shufps/eload2/images/PXL_20251216_090533911.jpg

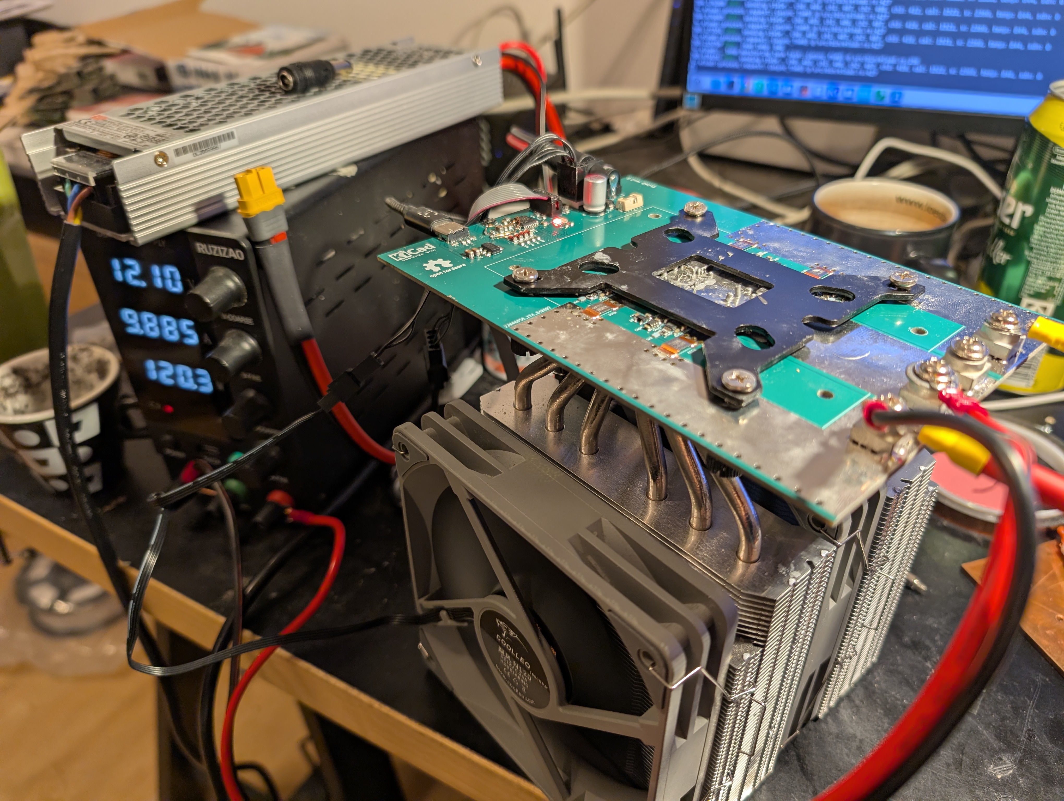
images/PXL_20251216_090533911.jpg
