shufps/eload2/firmware/stm32-metapac/src/chips/metadata_0062.rs

                pub(crate) static PERIPHERALS: &'static [Peripheral] = &[
    Peripheral {
        name: "ADC1",
        address: 1073816576,
        registers: Some(
            PeripheralRegisters {
                kind: "adc",
                version: "f1",
                block: "ADC",
                ir: &adc::REGISTERS,
            },
        ),
        rcc: Some(
            PeripheralRcc {
                clock: "pclk2",
                enable: Some(
                    PeripheralRccRegister {
                        register: "apb2enr",
                        field: "adc1en",
                    },
                ),
                reset: Some(
                    PeripheralRccRegister {
                        register: "apb2rstr",
                        field: "adc1rst",
                    },
                ),
                mux: None,
                stop_mode: StopMode::Stop1,
            },
        ),
        pins: &[
            PeripheralPin {
                pin: "PA0",
                signal: "IN0",
                af: None,
            },
            PeripheralPin {
                pin: "PA1",
                signal: "IN1",
                af: None,
            },
            PeripheralPin {
                pin: "PA2",
                signal: "IN2",
                af: None,
            },
            PeripheralPin {
                pin: "PA3",
                signal: "IN3",
                af: None,
            },
            PeripheralPin {
                pin: "PA4",
                signal: "IN4",
                af: None,
            },
            PeripheralPin {
                pin: "PA5",
                signal: "IN5",
                af: None,
            },
            PeripheralPin {
                pin: "PA6",
                signal: "IN6",
                af: None,
            },
            PeripheralPin {
                pin: "PA7",
                signal: "IN7",
                af: None,
            },
            PeripheralPin {
                pin: "PB0",
                signal: "IN8",
                af: None,
            },
            PeripheralPin {
                pin: "PB1",
                signal: "IN9",
                af: None,
            },
        ],
        dma_channels: &[
            PeripheralDmaChannel {
                signal: "ADC1",
                channel: Some(
                    "DMA1_CH1",
                ),
                dmamux: None,
                dma: None,
                request: None,
            },
        ],
        interrupts: &[
            PeripheralInterrupt {
                signal: "GLOBAL",
                interrupt: "ADC1",
            },
        ],
    },
    Peripheral {
        name: "ADC_COMMON",
        address: 1073816576,
        registers: None,
        rcc: None,
        pins: &[],
        dma_channels: &[],
        interrupts: &[],
    },
    Peripheral {
        name: "AFIO",
        address: 1073807360,
        registers: Some(
            PeripheralRegisters {
                kind: "afio",
                version: "f1",
                block: "AFIO",
                ir: &afio::REGISTERS,
            },
        ),
        rcc: Some(
            PeripheralRcc {
                clock: "pclk2",
                enable: Some(
                    PeripheralRccRegister {
                        register: "apb2enr",
                        field: "afioen",
                    },
                ),
                reset: Some(
                    PeripheralRccRegister {
                        register: "apb2rstr",
                        field: "afiorst",
                    },
                ),
                mux: None,
                stop_mode: StopMode::Stop1,
            },
        ),
        pins: &[],
        dma_channels: &[],
        interrupts: &[],
    },
    Peripheral {
        name: "BKP",
        address: 1073769472,
        registers: Some(
            PeripheralRegisters {
                kind: "bkp",
                version: "v1",
                block: "BKP",
                ir: &bkp::REGISTERS,
            },
        ),
        rcc: Some(
            PeripheralRcc {
                clock: "pclk1",
                enable: Some(
                    PeripheralRccRegister {
                        register: "apb1enr",
                        field: "bkpen",
                    },
                ),
                reset: Some(
                    PeripheralRccRegister {
                        register: "apb1rstr",
                        field: "bkprst",
                    },
                ),
                mux: None,
                stop_mode: StopMode::Stop1,
            },
        ),
        pins: &[],
        dma_channels: &[],
        interrupts: &[],
    },
    Peripheral {
        name: "CEC",
        address: 1073772544,
        registers: None,
        rcc: Some(
            PeripheralRcc {
                clock: "pclk1",
                enable: Some(
                    PeripheralRccRegister {
                        register: "apb1enr",
                        field: "cecen",
                    },
                ),
                reset: Some(
                    PeripheralRccRegister {
                        register: "apb1rstr",
                        field: "cecrst",
                    },
                ),
                mux: None,
                stop_mode: StopMode::Stop1,
            },
        ),
        pins: &[],
        dma_channels: &[],
        interrupts: &[],
    },
    Peripheral {
        name: "CRC",
        address: 1073885184,
        registers: Some(
            PeripheralRegisters {
                kind: "crc",
                version: "v1",
                block: "CRC",
                ir: &crc::REGISTERS,
            },
        ),
        rcc: Some(
            PeripheralRcc {
                clock: "hclk1",
                enable: Some(
                    PeripheralRccRegister {
                        register: "ahbenr",
                        field: "crcen",
                    },
                ),
                reset: None,
                mux: None,
                stop_mode: StopMode::Stop1,
            },
        ),
        pins: &[],
        dma_channels: &[],
        interrupts: &[],
    },
    Peripheral {
        name: "DAC",
        address: 1073771520,
        registers: Some(
            PeripheralRegisters {
                kind: "dac",
                version: "v2",
                block: "DAC",
                ir: &dac::REGISTERS,
            },
        ),
        rcc: Some(
            PeripheralRcc {
                clock: "pclk1",
                enable: Some(
                    PeripheralRccRegister {
                        register: "apb1enr",
                        field: "dacen",
                    },
                ),
                reset: Some(
                    PeripheralRccRegister {
                        register: "apb1rstr",
                        field: "dacrst",
                    },
                ),
                mux: None,
                stop_mode: StopMode::Stop1,
            },
        ),
        pins: &[
            PeripheralPin {
                pin: "PA4",
                signal: "OUT1",
                af: None,
            },
            PeripheralPin {
                pin: "PA5",
                signal: "OUT2",
                af: None,
            },
        ],
        dma_channels: &[
            PeripheralDmaChannel {
                signal: "CH1",
                channel: Some(
                    "DMA1_CH3",
                ),
                dmamux: None,
                dma: None,
                request: None,
            },
            PeripheralDmaChannel {
                signal: "CH2",
                channel: Some(
                    "DMA1_CH4",
                ),
                dmamux: None,
                dma: None,
                request: None,
            },
        ],
        interrupts: &[
            PeripheralInterrupt {
                signal: "GLOBAL",
                interrupt: "TIM6_DAC",
            },
        ],
    },
    Peripheral {
        name: "DBGMCU",
        address: 3758366720,
        registers: Some(
            PeripheralRegisters {
                kind: "dbgmcu",
                version: "f1",
                block: "DBGMCU",
                ir: &dbgmcu::REGISTERS,
            },
        ),
        rcc: None,
        pins: &[],
        dma_channels: &[],
        interrupts: &[],
    },
    Peripheral {
        name: "DMA1",
        address: 1073872896,
        registers: Some(
            PeripheralRegisters {
                kind: "bdma",
                version: "v1",
                block: "DMA",
                ir: &bdma::REGISTERS,
            },
        ),
        rcc: Some(
            PeripheralRcc {
                clock: "hclk1",
                enable: Some(
                    PeripheralRccRegister {
                        register: "ahbenr",
                        field: "dma1en",
                    },
                ),
                reset: None,
                mux: None,
                stop_mode: StopMode::Stop1,
            },
        ),
        pins: &[],
        dma_channels: &[],
        interrupts: &[
            PeripheralInterrupt {
                signal: "CH1",
                interrupt: "DMA1_CHANNEL1",
            },
            PeripheralInterrupt {
                signal: "CH2",
                interrupt: "DMA1_CHANNEL2",
            },
            PeripheralInterrupt {
                signal: "CH3",
                interrupt: "DMA1_CHANNEL3",
            },
            PeripheralInterrupt {
                signal: "CH4",
                interrupt: "DMA1_CHANNEL4",
            },
            PeripheralInterrupt {
                signal: "CH5",
                interrupt: "DMA1_CHANNEL5",
            },
            PeripheralInterrupt {
                signal: "CH6",
                interrupt: "DMA1_CHANNEL6",
            },
            PeripheralInterrupt {
                signal: "CH7",
                interrupt: "DMA1_CHANNEL7",
            },
        ],
    },
    Peripheral {
        name: "EXTI",
        address: 1073808384,
        registers: Some(
            PeripheralRegisters {
                kind: "exti",
                version: "v1",
                block: "EXTI",
                ir: &exti::REGISTERS,
            },
        ),
        rcc: None,
        pins: &[],
        dma_channels: &[],
        interrupts: &[
            PeripheralInterrupt {
                signal: "EXTI0",
                interrupt: "EXTI0",
            },
            PeripheralInterrupt {
                signal: "EXTI1",
                interrupt: "EXTI1",
            },
            PeripheralInterrupt {
                signal: "EXTI10",
                interrupt: "EXTI15_10",
            },
            PeripheralInterrupt {
                signal: "EXTI11",
                interrupt: "EXTI15_10",
            },
            PeripheralInterrupt {
                signal: "EXTI12",
                interrupt: "EXTI15_10",
            },
            PeripheralInterrupt {
                signal: "EXTI13",
                interrupt: "EXTI15_10",
            },
            PeripheralInterrupt {
                signal: "EXTI14",
                interrupt: "EXTI15_10",
            },
            PeripheralInterrupt {
                signal: "EXTI15",
                interrupt: "EXTI15_10",
            },
            PeripheralInterrupt {
                signal: "EXTI2",
                interrupt: "EXTI2",
            },
            PeripheralInterrupt {
                signal: "EXTI3",
                interrupt: "EXTI3",
            },
            PeripheralInterrupt {
                signal: "EXTI4",
                interrupt: "EXTI4",
            },
            PeripheralInterrupt {
                signal: "EXTI5",
                interrupt: "EXTI9_5",
            },
            PeripheralInterrupt {
                signal: "EXTI6",
                interrupt: "EXTI9_5",
            },
            PeripheralInterrupt {
                signal: "EXTI7",
                interrupt: "EXTI9_5",
            },
            PeripheralInterrupt {
                signal: "EXTI8",
                interrupt: "EXTI9_5",
            },
            PeripheralInterrupt {
                signal: "EXTI9",
                interrupt: "EXTI9_5",
            },
        ],
    },
    Peripheral {
        name: "FLASH",
        address: 1073881088,
        registers: Some(
            PeripheralRegisters {
                kind: "flash",
                version: "f1",
                block: "FLASH",
                ir: &flash::REGISTERS,
            },
        ),
        rcc: Some(
            PeripheralRcc {
                clock: "hclk1",
                enable: Some(
                    PeripheralRccRegister {
                        register: "ahbenr",
                        field: "flashen",
                    },
                ),
                reset: None,
                mux: None,
                stop_mode: StopMode::Stop1,
            },
        ),
        pins: &[],
        dma_channels: &[],
        interrupts: &[
            PeripheralInterrupt {
                signal: "GLOBAL",
                interrupt: "FLASH",
            },
        ],
    },
    Peripheral {
        name: "GPIOA",
        address: 1073809408,
        registers: Some(
            PeripheralRegisters {
                kind: "gpio",
                version: "v1",
                block: "GPIO",
                ir: &gpio::REGISTERS,
            },
        ),
        rcc: Some(
            PeripheralRcc {
                clock: "pclk2",
                enable: Some(
                    PeripheralRccRegister {
                        register: "apb2enr",
                        field: "gpioaen",
                    },
                ),
                reset: Some(
                    PeripheralRccRegister {
                        register: "apb2rstr",
                        field: "gpioarst",
                    },
                ),
                mux: None,
                stop_mode: StopMode::Stop1,
            },
        ),
        pins: &[],
        dma_channels: &[],
        interrupts: &[],
    },
    Peripheral {
        name: "GPIOB",
        address: 1073810432,
        registers: Some(
            PeripheralRegisters {
                kind: "gpio",
                version: "v1",
                block: "GPIO",
                ir: &gpio::REGISTERS,
            },
        ),
        rcc: Some(
            PeripheralRcc {
                clock: "pclk2",
                enable: Some(
                    PeripheralRccRegister {
                        register: "apb2enr",
                        field: "gpioben",
                    },
                ),
                reset: Some(
                    PeripheralRccRegister {
                        register: "apb2rstr",
                        field: "gpiobrst",
                    },
                ),
                mux: None,
                stop_mode: StopMode::Stop1,
            },
        ),
        pins: &[],
        dma_channels: &[],
        interrupts: &[],
    },
    Peripheral {
        name: "GPIOC",
        address: 1073811456,
        registers: Some(
            PeripheralRegisters {
                kind: "gpio",
                version: "v1",
                block: "GPIO",
                ir: &gpio::REGISTERS,
            },
        ),
        rcc: Some(
            PeripheralRcc {
                clock: "pclk2",
                enable: Some(
                    PeripheralRccRegister {
                        register: "apb2enr",
                        field: "gpiocen",
                    },
                ),
                reset: Some(
                    PeripheralRccRegister {
                        register: "apb2rstr",
                        field: "gpiocrst",
                    },
                ),
                mux: None,
                stop_mode: StopMode::Stop1,
            },
        ),
        pins: &[],
        dma_channels: &[],
        interrupts: &[],
    },
    Peripheral {
        name: "GPIOD",
        address: 1073812480,
        registers: Some(
            PeripheralRegisters {
                kind: "gpio",
                version: "v1",
                block: "GPIO",
                ir: &gpio::REGISTERS,
            },
        ),
        rcc: Some(
            PeripheralRcc {
                clock: "pclk2",
                enable: Some(
                    PeripheralRccRegister {
                        register: "apb2enr",
                        field: "gpioden",
                    },
                ),
                reset: Some(
                    PeripheralRccRegister {
                        register: "apb2rstr",
                        field: "gpiodrst",
                    },
                ),
                mux: None,
                stop_mode: StopMode::Stop1,
            },
        ),
        pins: &[],
        dma_channels: &[],
        interrupts: &[],
    },
    Peripheral {
        name: "GPIOE",
        address: 1073813504,
        registers: Some(
            PeripheralRegisters {
                kind: "gpio",
                version: "v1",
                block: "GPIO",
                ir: &gpio::REGISTERS,
            },
        ),
        rcc: Some(
            PeripheralRcc {
                clock: "pclk2",
                enable: Some(
                    PeripheralRccRegister {
                        register: "apb2enr",
                        field: "gpioeen",
                    },
                ),
                reset: Some(
                    PeripheralRccRegister {
                        register: "apb2rstr",
                        field: "gpioerst",
                    },
                ),
                mux: None,
                stop_mode: StopMode::Stop1,
            },
        ),
        pins: &[],
        dma_channels: &[],
        interrupts: &[],
    },
    Peripheral {
        name: "I2C1",
        address: 1073763328,
        registers: Some(
            PeripheralRegisters {
                kind: "i2c",
                version: "v1",
                block: "I2C",
                ir: &i2c::REGISTERS,
            },
        ),
        rcc: Some(
            PeripheralRcc {
                clock: "pclk1",
                enable: Some(
                    PeripheralRccRegister {
                        register: "apb1enr",
                        field: "i2c1en",
                    },
                ),
                reset: Some(
                    PeripheralRccRegister {
                        register: "apb1rstr",
                        field: "i2c1rst",
                    },
                ),
                mux: None,
                stop_mode: StopMode::Stop1,
            },
        ),
        pins: &[
            PeripheralPin {
                pin: "PB5",
                signal: "SMBA",
                af: None,
            },
            PeripheralPin {
                pin: "PB6",
                signal: "SCL",
                af: None,
            },
            PeripheralPin {
                pin: "PB7",
                signal: "SDA",
                af: None,
            },
            PeripheralPin {
                pin: "PB8",
                signal: "SCL",
                af: None,
            },
            PeripheralPin {
                pin: "PB9",
                signal: "SDA",
                af: None,
            },
        ],
        dma_channels: &[
            PeripheralDmaChannel {
                signal: "TX",
                channel: Some(
                    "DMA1_CH6",
                ),
                dmamux: None,
                dma: None,
                request: None,
            },
            PeripheralDmaChannel {
                signal: "RX",
                channel: Some(
                    "DMA1_CH7",
                ),
                dmamux: None,
                dma: None,
                request: None,
            },
        ],
        interrupts: &[
            PeripheralInterrupt {
                signal: "ER",
                interrupt: "I2C1_ER",
            },
            PeripheralInterrupt {
                signal: "EV",
                interrupt: "I2C1_EV",
            },
        ],
    },
    Peripheral {
        name: "IWDG",
        address: 1073754112,
        registers: Some(
            PeripheralRegisters {
                kind: "iwdg",
                version: "v1",
                block: "IWDG",
                ir: &iwdg::REGISTERS,
            },
        ),
        rcc: None,
        pins: &[],
        dma_channels: &[],
        interrupts: &[],
    },
    Peripheral {
        name: "PWR",
        address: 1073770496,
        registers: Some(
            PeripheralRegisters {
                kind: "pwr",
                version: "f1",
                block: "PWR",
                ir: &pwr::REGISTERS,
            },
        ),
        rcc: Some(
            PeripheralRcc {
                clock: "pclk1",
                enable: Some(
                    PeripheralRccRegister {
                        register: "apb1enr",
                        field: "pwren",
                    },
                ),
                reset: Some(
                    PeripheralRccRegister {
                        register: "apb1rstr",
                        field: "pwrrst",
                    },
                ),
                mux: None,
                stop_mode: StopMode::Stop1,
            },
        ),
        pins: &[],
        dma_channels: &[],
        interrupts: &[],
    },
    Peripheral {
        name: "RCC",
        address: 1073876992,
        registers: Some(
            PeripheralRegisters {
                kind: "rcc",
                version: "f100",
                block: "RCC",
                ir: &rcc::REGISTERS,
            },
        ),
        rcc: None,
        pins: &[
            PeripheralPin {
                pin: "PA8",
                signal: "MCO",
                af: None,
            },
            PeripheralPin {
                pin: "PC14",
                signal: "OSC32_IN",
                af: None,
            },
            PeripheralPin {
                pin: "PC15",
                signal: "OSC32_OUT",
                af: None,
            },
            PeripheralPin {
                pin: "PD0",
                signal: "OSC_IN",
                af: None,
            },
            PeripheralPin {
                pin: "PD1",
                signal: "OSC_OUT",
                af: None,
            },
        ],
        dma_channels: &[],
        interrupts: &[
            PeripheralInterrupt {
                signal: "GLOBAL",
                interrupt: "RCC",
            },
        ],
    },
    Peripheral {
        name: "RTC",
        address: 1073752064,
        registers: Some(
            PeripheralRegisters {
                kind: "rtc",
                version: "v1",
                block: "RTC",
                ir: &rtc::REGISTERS,
            },
        ),
        rcc: None,
        pins: &[
            PeripheralPin {
                pin: "PC13",
                signal: "OUT",
                af: None,
            },
            PeripheralPin {
                pin: "PC13",
                signal: "TAMPER",
                af: None,
            },
        ],
        dma_channels: &[],
        interrupts: &[
            PeripheralInterrupt {
                signal: "ALARM",
                interrupt: "RTC_ALARM",
            },
            PeripheralInterrupt {
                signal: "SSRU",
                interrupt: "RTC",
            },
            PeripheralInterrupt {
                signal: "STAMP",
                interrupt: "RTC",
            },
            PeripheralInterrupt {
                signal: "TAMP",
                interrupt: "TAMPER",
            },
            PeripheralInterrupt {
                signal: "WKUP",
                interrupt: "RTC",
            },
        ],
    },
    Peripheral {
        name: "SPI1",
        address: 1073819648,
        registers: Some(
            PeripheralRegisters {
                kind: "spi",
                version: "f1",
                block: "SPI",
                ir: &spi::REGISTERS,
            },
        ),
        rcc: Some(
            PeripheralRcc {
                clock: "pclk2",
                enable: Some(
                    PeripheralRccRegister {
                        register: "apb2enr",
                        field: "spi1en",
                    },
                ),
                reset: Some(
                    PeripheralRccRegister {
                        register: "apb2rstr",
                        field: "spi1rst",
                    },
                ),
                mux: None,
                stop_mode: StopMode::Stop1,
            },
        ),
        pins: &[
            PeripheralPin {
                pin: "PA15",
                signal: "NSS",
                af: None,
            },
            PeripheralPin {
                pin: "PA4",
                signal: "NSS",
                af: None,
            },
            PeripheralPin {
                pin: "PA5",
                signal: "SCK",
                af: None,
            },
            PeripheralPin {
                pin: "PA6",
                signal: "MISO",
                af: None,
            },
            PeripheralPin {
                pin: "PA7",
                signal: "MOSI",
                af: None,
            },
            PeripheralPin {
                pin: "PB3",
                signal: "SCK",
                af: None,
            },
            PeripheralPin {
                pin: "PB4",
                signal: "MISO",
                af: None,
            },
            PeripheralPin {
                pin: "PB5",
                signal: "MOSI",
                af: None,
            },
        ],
        dma_channels: &[
            PeripheralDmaChannel {
                signal: "RX",
                channel: Some(
                    "DMA1_CH2",
                ),
                dmamux: None,
                dma: None,
                request: None,
            },
            PeripheralDmaChannel {
                signal: "TX",
                channel: Some(
                    "DMA1_CH3",
                ),
                dmamux: None,
                dma: None,
                request: None,
            },
        ],
        interrupts: &[
            PeripheralInterrupt {
                signal: "GLOBAL",
                interrupt: "SPI1",
            },
        ],
    },
    Peripheral {
        name: "TIM1",
        address: 1073818624,
        registers: Some(
            PeripheralRegisters {
                kind: "timer",
                version: "v1",
                block: "TIM_ADV",
                ir: &timer::REGISTERS,
            },
        ),
        rcc: Some(
            PeripheralRcc {
                clock: "pclk2_tim",
                enable: Some(
                    PeripheralRccRegister {
                        register: "apb2enr",
                        field: "tim1en",
                    },
                ),
                reset: Some(
                    PeripheralRccRegister {
                        register: "apb2rstr",
                        field: "tim1rst",
                    },
                ),
                mux: None,
                stop_mode: StopMode::Stop1,
            },
        ),
        pins: &[
            PeripheralPin {
                pin: "PA10",
                signal: "CH3",
                af: None,
            },
            PeripheralPin {
                pin: "PA11",
                signal: "CH4",
                af: None,
            },
            PeripheralPin {
                pin: "PA12",
                signal: "ETR",
                af: None,
            },
            PeripheralPin {
                pin: "PA6",
                signal: "BKIN",
                af: None,
            },
            PeripheralPin {
                pin: "PA7",
                signal: "CH1N",
                af: None,
            },
            PeripheralPin {
                pin: "PA8",
                signal: "CH1",
                af: None,
            },
            PeripheralPin {
                pin: "PA9",
                signal: "CH2",
                af: None,
            },
            PeripheralPin {
                pin: "PB0",
                signal: "CH2N",
                af: None,
            },
            PeripheralPin {
                pin: "PB1",
                signal: "CH3N",
                af: None,
            },
            PeripheralPin {
                pin: "PB12",
                signal: "BKIN",
                af: None,
            },
            PeripheralPin {
                pin: "PB13",
                signal: "CH1N",
                af: None,
            },
            PeripheralPin {
                pin: "PB14",
                signal: "CH2N",
                af: None,
            },
            PeripheralPin {
                pin: "PB15",
                signal: "CH3N",
                af: None,
            },
        ],
        dma_channels: &[
            PeripheralDmaChannel {
                signal: "CH1",
                channel: Some(
                    "DMA1_CH2",
                ),
                dmamux: None,
                dma: None,
                request: None,
            },
            PeripheralDmaChannel {
                signal: "CH2",
                channel: Some(
                    "DMA1_CH3",
                ),
                dmamux: None,
                dma: None,
                request: None,
            },
            PeripheralDmaChannel {
                signal: "CH4",
                channel: Some(
                    "DMA1_CH4",
                ),
                dmamux: None,
                dma: None,
                request: None,
            },
            PeripheralDmaChannel {
                signal: "TRIG",
                channel: Some(
                    "DMA1_CH4",
                ),
                dmamux: None,
                dma: None,
                request: None,
            },
            PeripheralDmaChannel {
                signal: "COM",
                channel: Some(
                    "DMA1_CH4",
                ),
                dmamux: None,
                dma: None,
                request: None,
            },
            PeripheralDmaChannel {
                signal: "UP",
                channel: Some(
                    "DMA1_CH5",
                ),
                dmamux: None,
                dma: None,
                request: None,
            },
            PeripheralDmaChannel {
                signal: "CH3",
                channel: Some(
                    "DMA1_CH6",
                ),
                dmamux: None,
                dma: None,
                request: None,
            },
            PeripheralDmaChannel {
                signal: "CH1",
                channel: Some(
                    "DMA1_CH6",
                ),
                dmamux: None,
                dma: None,
                request: None,
            },
            PeripheralDmaChannel {
                signal: "CH2",
                channel: Some(
                    "DMA1_CH6",
                ),
                dmamux: None,
                dma: None,
                request: None,
            },
            PeripheralDmaChannel {
                signal: "CH3",
                channel: Some(
                    "DMA1_CH6",
                ),
                dmamux: None,
                dma: None,
                request: None,
            },
        ],
        interrupts: &[
            PeripheralInterrupt {
                signal: "BRK",
                interrupt: "TIM1_BRK_TIM15",
            },
            PeripheralInterrupt {
                signal: "CC",
                interrupt: "TIM1_CC",
            },
            PeripheralInterrupt {
                signal: "COM",
                interrupt: "TIM1_TRG_COM_TIM17",
            },
            PeripheralInterrupt {
                signal: "TRG",
                interrupt: "TIM1_TRG_COM_TIM17",
            },
            PeripheralInterrupt {
                signal: "UP",
                interrupt: "TIM1_UP_TIM16",
            },
        ],
    },
    Peripheral {
        name: "TIM15",
        address: 1073823744,
        registers: Some(
            PeripheralRegisters {
                kind: "timer",
                version: "v1",
                block: "TIM_GP16",
                ir: &timer::REGISTERS,
            },
        ),
        rcc: Some(
            PeripheralRcc {
                clock: "pclk2_tim",
                enable: Some(
                    PeripheralRccRegister {
                        register: "apb2enr",
                        field: "tim15en",
                    },
                ),
                reset: Some(
                    PeripheralRccRegister {
                        register: "apb2rstr",
                        field: "tim15rst",
                    },
                ),
                mux: None,
                stop_mode: StopMode::Stop1,
            },
        ),
        pins: &[
            PeripheralPin {
                pin: "PA2",
                signal: "CH1",
                af: None,
            },
            PeripheralPin {
                pin: "PA3",
                signal: "CH2",
                af: None,
            },
            PeripheralPin {
                pin: "PA9",
                signal: "BKIN",
                af: None,
            },
            PeripheralPin {
                pin: "PB14",
                signal: "CH1",
                af: None,
            },
            PeripheralPin {
                pin: "PB15",
                signal: "CH1N",
                af: None,
            },
            PeripheralPin {
                pin: "PB15",
                signal: "CH2",
                af: None,
            },
        ],
        dma_channels: &[
            PeripheralDmaChannel {
                signal: "CH1",
                channel: Some(
                    "DMA1_CH5",
                ),
                dmamux: None,
                dma: None,
                request: None,
            },
            PeripheralDmaChannel {
                signal: "UP",
                channel: Some(
                    "DMA1_CH5",
                ),
                dmamux: None,
                dma: None,
                request: None,
            },
            PeripheralDmaChannel {
                signal: "TRIG",
                channel: Some(
                    "DMA1_CH5",
                ),
                dmamux: None,
                dma: None,
                request: None,
            },
            PeripheralDmaChannel {
                signal: "COM",
                channel: Some(
                    "DMA1_CH5",
                ),
                dmamux: None,
                dma: None,
                request: None,
            },
        ],
        interrupts: &[
            PeripheralInterrupt {
                signal: "BRK",
                interrupt: "TIM1_BRK_TIM15",
            },
            PeripheralInterrupt {
                signal: "CC",
                interrupt: "TIM1_BRK_TIM15",
            },
            PeripheralInterrupt {
                signal: "COM",
                interrupt: "TIM1_BRK_TIM15",
            },
            PeripheralInterrupt {
                signal: "TRG",
                interrupt: "TIM1_BRK_TIM15",
            },
            PeripheralInterrupt {
                signal: "UP",
                interrupt: "TIM1_BRK_TIM15",
            },
        ],
    },
    Peripheral {
        name: "TIM16",
        address: 1073824768,
        registers: Some(
            PeripheralRegisters {
                kind: "timer",
                version: "v1",
                block: "TIM_GP16",
                ir: &timer::REGISTERS,
            },
        ),
        rcc: Some(
            PeripheralRcc {
                clock: "pclk2_tim",
                enable: Some(
                    PeripheralRccRegister {
                        register: "apb2enr",
                        field: "tim16en",
                    },
                ),
                reset: Some(
                    PeripheralRccRegister {
                        register: "apb2rstr",
                        field: "tim16rst",
                    },
                ),
                mux: None,
                stop_mode: StopMode::Stop1,
            },
        ),
        pins: &[
            PeripheralPin {
                pin: "PA6",
                signal: "CH1",
                af: None,
            },
            PeripheralPin {
                pin: "PB5",
                signal: "BKIN",
                af: None,
            },
            PeripheralPin {
                pin: "PB6",
                signal: "CH1N",
                af: None,
            },
            PeripheralPin {
                pin: "PB8",
                signal: "CH1",
                af: None,
            },
        ],
        dma_channels: &[
            PeripheralDmaChannel {
                signal: "CH1",
                channel: Some(
                    "DMA1_CH6",
                ),
                dmamux: None,
                dma: None,
                request: None,
            },
            PeripheralDmaChannel {
                signal: "UP",
                channel: Some(
                    "DMA1_CH6",
                ),
                dmamux: None,
                dma: None,
                request: None,
            },
        ],
        interrupts: &[
            PeripheralInterrupt {
                signal: "BRK",
                interrupt: "TIM1_UP_TIM16",
            },
            PeripheralInterrupt {
                signal: "CC",
                interrupt: "TIM1_UP_TIM16",
            },
            PeripheralInterrupt {
                signal: "COM",
                interrupt: "TIM1_UP_TIM16",
            },
            PeripheralInterrupt {
                signal: "TRG",
                interrupt: "TIM1_UP_TIM16",
            },
            PeripheralInterrupt {
                signal: "UP",
                interrupt: "TIM1_UP_TIM16",
            },
        ],
    },
    Peripheral {
        name: "TIM17",
        address: 1073825792,
        registers: Some(
            PeripheralRegisters {
                kind: "timer",
                version: "v1",
                block: "TIM_GP16",
                ir: &timer::REGISTERS,
            },
        ),
        rcc: Some(
            PeripheralRcc {
                clock: "pclk2_tim",
                enable: Some(
                    PeripheralRccRegister {
                        register: "apb2enr",
                        field: "tim17en",
                    },
                ),
                reset: Some(
                    PeripheralRccRegister {
                        register: "apb2rstr",
                        field: "tim17rst",
                    },
                ),
                mux: None,
                stop_mode: StopMode::Stop1,
            },
        ),
        pins: &[
            PeripheralPin {
                pin: "PA10",
                signal: "BKIN",
                af: None,
            },
            PeripheralPin {
                pin: "PA7",
                signal: "CH1",
                af: None,
            },
            PeripheralPin {
                pin: "PB7",
                signal: "CH1N",
                af: None,
            },
            PeripheralPin {
                pin: "PB9",
                signal: "CH1",
                af: None,
            },
        ],
        dma_channels: &[
            PeripheralDmaChannel {
                signal: "CH1",
                channel: Some(
                    "DMA1_CH7",
                ),
                dmamux: None,
                dma: None,
                request: None,
            },
            PeripheralDmaChannel {
                signal: "UP",
                channel: Some(
                    "DMA1_CH7",
                ),
                dmamux: None,
                dma: None,
                request: None,
            },
        ],
        interrupts: &[
            PeripheralInterrupt {
                signal: "BRK",
                interrupt: "TIM1_TRG_COM_TIM17",
            },
            PeripheralInterrupt {
                signal: "CC",
                interrupt: "TIM1_TRG_COM_TIM17",
            },
            PeripheralInterrupt {
                signal: "COM",
                interrupt: "TIM1_TRG_COM_TIM17",
            },
            PeripheralInterrupt {
                signal: "TRG",
                interrupt: "TIM1_TRG_COM_TIM17",
            },
            PeripheralInterrupt {
                signal: "UP",
                interrupt: "TIM1_TRG_COM_TIM17",
            },
        ],
    },
    Peripheral {
        name: "TIM2",
        address: 1073741824,
        registers: Some(
            PeripheralRegisters {
                kind: "timer",
                version: "v1",
                block: "TIM_GP16",
                ir: &timer::REGISTERS,
            },
        ),
        rcc: Some(
            PeripheralRcc {
                clock: "pclk1_tim",
                enable: Some(
                    PeripheralRccRegister {
                        register: "apb1enr",
                        field: "tim2en",
                    },
                ),
                reset: Some(
                    PeripheralRccRegister {
                        register: "apb1rstr",
                        field: "tim2rst",
                    },
                ),
                mux: None,
                stop_mode: StopMode::Stop1,
            },
        ),
        pins: &[
            PeripheralPin {
                pin: "PA0",
                signal: "CH1",
                af: None,
            },
            PeripheralPin {
                pin: "PA0",
                signal: "ETR",
                af: None,
            },
            PeripheralPin {
                pin: "PA1",
                signal: "CH2",
                af: None,
            },
            PeripheralPin {
                pin: "PA15",
                signal: "CH1",
                af: None,
            },
            PeripheralPin {
                pin: "PA15",
                signal: "ETR",
                af: None,
            },
            PeripheralPin {
                pin: "PA2",
                signal: "CH3",
                af: None,
            },
            PeripheralPin {
                pin: "PA3",
                signal: "CH4",
                af: None,
            },
            PeripheralPin {
                pin: "PB10",
                signal: "CH3",
                af: None,
            },
            PeripheralPin {
                pin: "PB11",
                signal: "CH4",
                af: None,
            },
            PeripheralPin {
                pin: "PB3",
                signal: "CH2",
                af: None,
            },
        ],
        dma_channels: &[
            PeripheralDmaChannel {
                signal: "CH3",
                channel: Some(
                    "DMA1_CH1",
                ),
                dmamux: None,
                dma: None,
                request: None,
            },
            PeripheralDmaChannel {
                signal: "UP",
                channel: Some(
                    "DMA1_CH2",
                ),
                dmamux: None,
                dma: None,
                request: None,
            },
            PeripheralDmaChannel {
                signal: "CH1",
                channel: Some(
                    "DMA1_CH5",
                ),
                dmamux: None,
                dma: None,
                request: None,
            },
            PeripheralDmaChannel {
                signal: "CH2",
                channel: Some(
                    "DMA1_CH7",
                ),
                dmamux: None,
                dma: None,
                request: None,
            },
            PeripheralDmaChannel {
                signal: "CH4",
                channel: Some(
                    "DMA1_CH7",
                ),
                dmamux: None,
                dma: None,
                request: None,
            },
        ],
        interrupts: &[
            PeripheralInterrupt {
                signal: "BRK",
                interrupt: "TIM2",
            },
            PeripheralInterrupt {
                signal: "CC",
                interrupt: "TIM2",
            },
            PeripheralInterrupt {
                signal: "COM",
                interrupt: "TIM2",
            },
            PeripheralInterrupt {
                signal: "TRG",
                interrupt: "TIM2",
            },
            PeripheralInterrupt {
                signal: "UP",
                interrupt: "TIM2",
            },
        ],
    },
    Peripheral {
        name: "TIM3",
        address: 1073742848,
        registers: Some(
            PeripheralRegisters {
                kind: "timer",
                version: "v1",
                block: "TIM_GP16",
                ir: &timer::REGISTERS,
            },
        ),
        rcc: Some(
            PeripheralRcc {
                clock: "pclk1_tim",
                enable: Some(
                    PeripheralRccRegister {
                        register: "apb1enr",
                        field: "tim3en",
                    },
                ),
                reset: Some(
                    PeripheralRccRegister {
                        register: "apb1rstr",
                        field: "tim3rst",
                    },
                ),
                mux: None,
                stop_mode: StopMode::Stop1,
            },
        ),
        pins: &[
            PeripheralPin {
                pin: "PA6",
                signal: "CH1",
                af: None,
            },
            PeripheralPin {
                pin: "PA7",
                signal: "CH2",
                af: None,
            },
            PeripheralPin {
                pin: "PB0",
                signal: "CH3",
                af: None,
            },
            PeripheralPin {
                pin: "PB1",
                signal: "CH4",
                af: None,
            },
            PeripheralPin {
                pin: "PB4",
                signal: "CH1",
                af: None,
            },
            PeripheralPin {
                pin: "PB5",
                signal: "CH2",
                af: None,
            },
        ],
        dma_channels: &[
            PeripheralDmaChannel {
                signal: "CH3",
                channel: Some(
                    "DMA1_CH2",
                ),
                dmamux: None,
                dma: None,
                request: None,
            },
            PeripheralDmaChannel {
                signal: "CH4",
                channel: Some(
                    "DMA1_CH3",
                ),
                dmamux: None,
                dma: None,
                request: None,
            },
            PeripheralDmaChannel {
                signal: "UP",
                channel: Some(
                    "DMA1_CH3",
                ),
                dmamux: None,
                dma: None,
                request: None,
            },
            PeripheralDmaChannel {
                signal: "CH1",
                channel: Some(
                    "DMA1_CH6",
                ),
                dmamux: None,
                dma: None,
                request: None,
            },
            PeripheralDmaChannel {
                signal: "TRIG",
                channel: Some(
                    "DMA1_CH6",
                ),
                dmamux: None,
                dma: None,
                request: None,
            },
        ],
        interrupts: &[
            PeripheralInterrupt {
                signal: "BRK",
                interrupt: "TIM3",
            },
            PeripheralInterrupt {
                signal: "CC",
                interrupt: "TIM3",
            },
            PeripheralInterrupt {
                signal: "COM",
                interrupt: "TIM3",
            },
            PeripheralInterrupt {
                signal: "TRG",
                interrupt: "TIM3",
            },
            PeripheralInterrupt {
                signal: "UP",
                interrupt: "TIM3",
            },
        ],
    },
    Peripheral {
        name: "TIM6",
        address: 1073745920,
        registers: Some(
            PeripheralRegisters {
                kind: "timer",
                version: "v1",
                block: "TIM_BASIC",
                ir: &timer::REGISTERS,
            },
        ),
        rcc: Some(
            PeripheralRcc {
                clock: "pclk1_tim",
                enable: Some(
                    PeripheralRccRegister {
                        register: "apb1enr",
                        field: "tim6en",
                    },
                ),
                reset: Some(
                    PeripheralRccRegister {
                        register: "apb1rstr",
                        field: "tim6rst",
                    },
                ),
                mux: None,
                stop_mode: StopMode::Stop1,
            },
        ),
        pins: &[],
        dma_channels: &[
            PeripheralDmaChannel {
                signal: "UP",
                channel: Some(
                    "DMA1_CH3",
                ),
                dmamux: None,
                dma: None,
                request: None,
            },
        ],
        interrupts: &[
            PeripheralInterrupt {
                signal: "BRK",
                interrupt: "TIM6_DAC",
            },
            PeripheralInterrupt {
                signal: "CC",
                interrupt: "TIM6_DAC",
            },
            PeripheralInterrupt {
                signal: "COM",
                interrupt: "TIM6_DAC",
            },
            PeripheralInterrupt {
                signal: "TRG",
                interrupt: "TIM6_DAC",
            },
            PeripheralInterrupt {
                signal: "UP",
                interrupt: "TIM6_DAC",
            },
        ],
    },
    Peripheral {
        name: "TIM7",
        address: 1073746944,
        registers: Some(
            PeripheralRegisters {
                kind: "timer",
                version: "v1",
                block: "TIM_BASIC",
                ir: &timer::REGISTERS,
            },
        ),
        rcc: Some(
            PeripheralRcc {
                clock: "pclk1_tim",
                enable: Some(
                    PeripheralRccRegister {
                        register: "apb1enr",
                        field: "tim7en",
                    },
                ),
                reset: Some(
                    PeripheralRccRegister {
                        register: "apb1rstr",
                        field: "tim7rst",
                    },
                ),
                mux: None,
                stop_mode: StopMode::Stop1,
            },
        ),
        pins: &[],
        dma_channels: &[
            PeripheralDmaChannel {
                signal: "UP",
                channel: Some(
                    "DMA1_CH4",
                ),
                dmamux: None,
                dma: None,
                request: None,
            },
        ],
        interrupts: &[
            PeripheralInterrupt {
                signal: "BRK",
                interrupt: "TIM7",
            },
            PeripheralInterrupt {
                signal: "CC",
                interrupt: "TIM7",
            },
            PeripheralInterrupt {
                signal: "COM",
                interrupt: "TIM7",
            },
            PeripheralInterrupt {
                signal: "TRG",
                interrupt: "TIM7",
            },
            PeripheralInterrupt {
                signal: "UP",
                interrupt: "TIM7",
            },
        ],
    },
    Peripheral {
        name: "UID",
        address: 536868840,
        registers: Some(
            PeripheralRegisters {
                kind: "uid",
                version: "v1",
                block: "UID",
                ir: &uid::REGISTERS,
            },
        ),
        rcc: None,
        pins: &[],
        dma_channels: &[],
        interrupts: &[],
    },
    Peripheral {
        name: "USART1",
        address: 1073821696,
        registers: Some(
            PeripheralRegisters {
                kind: "usart",
                version: "v1",
                block: "USART",
                ir: &usart::REGISTERS,
            },
        ),
        rcc: Some(
            PeripheralRcc {
                clock: "pclk2",
                enable: Some(
                    PeripheralRccRegister {
                        register: "apb2enr",
                        field: "usart1en",
                    },
                ),
                reset: Some(
                    PeripheralRccRegister {
                        register: "apb2rstr",
                        field: "usart1rst",
                    },
                ),
                mux: None,
                stop_mode: StopMode::Stop1,
            },
        ),
        pins: &[
            PeripheralPin {
                pin: "PA10",
                signal: "RX",
                af: None,
            },
            PeripheralPin {
                pin: "PA11",
                signal: "CTS",
                af: None,
            },
            PeripheralPin {
                pin: "PA12",
                signal: "RTS",
                af: None,
            },
            PeripheralPin {
                pin: "PA8",
                signal: "CK",
                af: None,
            },
            PeripheralPin {
                pin: "PA9",
                signal: "TX",
                af: None,
            },
            PeripheralPin {
                pin: "PB6",
                signal: "TX",
                af: None,
            },
            PeripheralPin {
                pin: "PB7",
                signal: "RX",
                af: None,
            },
        ],
        dma_channels: &[
            PeripheralDmaChannel {
                signal: "TX",
                channel: Some(
                    "DMA1_CH4",
                ),
                dmamux: None,
                dma: None,
                request: None,
            },
            PeripheralDmaChannel {
                signal: "RX",
                channel: Some(
                    "DMA1_CH5",
                ),
                dmamux: None,
                dma: None,
                request: None,
            },
        ],
        interrupts: &[
            PeripheralInterrupt {
                signal: "GLOBAL",
                interrupt: "USART1",
            },
        ],
    },
    Peripheral {
        name: "USART2",
        address: 1073759232,
        registers: Some(
            PeripheralRegisters {
                kind: "usart",
                version: "v1",
                block: "USART",
                ir: &usart::REGISTERS,
            },
        ),
        rcc: Some(
            PeripheralRcc {
                clock: "pclk1",
                enable: Some(
                    PeripheralRccRegister {
                        register: "apb1enr",
                        field: "usart2en",
                    },
                ),
                reset: Some(
                    PeripheralRccRegister {
                        register: "apb1rstr",
                        field: "usart2rst",
                    },
                ),
                mux: None,
                stop_mode: StopMode::Stop1,
            },
        ),
        pins: &[
            PeripheralPin {
                pin: "PA0",
                signal: "CTS",
                af: None,
            },
            PeripheralPin {
                pin: "PA1",
                signal: "RTS",
                af: None,
            },
            PeripheralPin {
                pin: "PA2",
                signal: "TX",
                af: None,
            },
            PeripheralPin {
                pin: "PA3",
                signal: "RX",
                af: None,
            },
            PeripheralPin {
                pin: "PA4",
                signal: "CK",
                af: None,
            },
        ],
        dma_channels: &[
            PeripheralDmaChannel {
                signal: "RX",
                channel: Some(
                    "DMA1_CH6",
                ),
                dmamux: None,
                dma: None,
                request: None,
            },
            PeripheralDmaChannel {
                signal: "TX",
                channel: Some(
                    "DMA1_CH7",
                ),
                dmamux: None,
                dma: None,
                request: None,
            },
        ],
        interrupts: &[
            PeripheralInterrupt {
                signal: "GLOBAL",
                interrupt: "USART2",
            },
        ],
    },
    Peripheral {
        name: "WWDG",
        address: 1073753088,
        registers: Some(
            PeripheralRegisters {
                kind: "wwdg",
                version: "v1",
                block: "WWDG",
                ir: &wwdg::REGISTERS,
            },
        ),
        rcc: Some(
            PeripheralRcc {
                clock: "pclk1",
                enable: Some(
                    PeripheralRccRegister {
                        register: "apb1enr",
                        field: "wwdgen",
                    },
                ),
                reset: Some(
                    PeripheralRccRegister {
                        register: "apb1rstr",
                        field: "wwdgrst",
                    },
                ),
                mux: None,
                stop_mode: StopMode::Stop1,
            },
        ),
        pins: &[],
        dma_channels: &[],
        interrupts: &[
            PeripheralInterrupt {
                signal: "GLOBAL",
                interrupt: "WWDG",
            },
            PeripheralInterrupt {
                signal: "RST",
                interrupt: "WWDG",
            },
        ],
    },
];
                pub(crate) static INTERRUPTS: &'static [Interrupt] = &[
    Interrupt {
        name: "WWDG",
        number: 0,
    },
    Interrupt {
        name: "PVD",
        number: 1,
    },
    Interrupt {
        name: "TAMPER",
        number: 2,
    },
    Interrupt {
        name: "RTC",
        number: 3,
    },
    Interrupt {
        name: "FLASH",
        number: 4,
    },
    Interrupt {
        name: "RCC",
        number: 5,
    },
    Interrupt {
        name: "EXTI0",
        number: 6,
    },
    Interrupt {
        name: "EXTI1",
        number: 7,
    },
    Interrupt {
        name: "EXTI2",
        number: 8,
    },
    Interrupt {
        name: "EXTI3",
        number: 9,
    },
    Interrupt {
        name: "EXTI4",
        number: 10,
    },
    Interrupt {
        name: "DMA1_CHANNEL1",
        number: 11,
    },
    Interrupt {
        name: "DMA1_CHANNEL2",
        number: 12,
    },
    Interrupt {
        name: "DMA1_CHANNEL3",
        number: 13,
    },
    Interrupt {
        name: "DMA1_CHANNEL4",
        number: 14,
    },
    Interrupt {
        name: "DMA1_CHANNEL5",
        number: 15,
    },
    Interrupt {
        name: "DMA1_CHANNEL6",
        number: 16,
    },
    Interrupt {
        name: "DMA1_CHANNEL7",
        number: 17,
    },
    Interrupt {
        name: "ADC1",
        number: 18,
    },
    Interrupt {
        name: "EXTI9_5",
        number: 23,
    },
    Interrupt {
        name: "TIM1_BRK_TIM15",
        number: 24,
    },
    Interrupt {
        name: "TIM1_UP_TIM16",
        number: 25,
    },
    Interrupt {
        name: "TIM1_TRG_COM_TIM17",
        number: 26,
    },
    Interrupt {
        name: "TIM1_CC",
        number: 27,
    },
    Interrupt {
        name: "TIM2",
        number: 28,
    },
    Interrupt {
        name: "TIM3",
        number: 29,
    },
    Interrupt {
        name: "TIM4",
        number: 30,
    },
    Interrupt {
        name: "I2C1_EV",
        number: 31,
    },
    Interrupt {
        name: "I2C1_ER",
        number: 32,
    },
    Interrupt {
        name: "I2C2_EV",
        number: 33,
    },
    Interrupt {
        name: "I2C2_ER",
        number: 34,
    },
    Interrupt {
        name: "SPI1",
        number: 35,
    },
    Interrupt {
        name: "SPI2",
        number: 36,
    },
    Interrupt {
        name: "USART1",
        number: 37,
    },
    Interrupt {
        name: "USART2",
        number: 38,
    },
    Interrupt {
        name: "USART3",
        number: 39,
    },
    Interrupt {
        name: "EXTI15_10",
        number: 40,
    },
    Interrupt {
        name: "RTC_ALARM",
        number: 41,
    },
    Interrupt {
        name: "CEC",
        number: 42,
    },
    Interrupt {
        name: "TIM6_DAC",
        number: 54,
    },
    Interrupt {
        name: "TIM7",
        number: 55,
    },
];
                pub(crate) static DMA_CHANNELS: &'static [DmaChannel] = &[
    DmaChannel {
        name: "DMA1_CH1",
        dma: "DMA1",
        channel: 0,
        dmamux: None,
        dmamux_channel: None,
    },
    DmaChannel {
        name: "DMA1_CH2",
        dma: "DMA1",
        channel: 1,
        dmamux: None,
        dmamux_channel: None,
    },
    DmaChannel {
        name: "DMA1_CH3",
        dma: "DMA1",
        channel: 2,
        dmamux: None,
        dmamux_channel: None,
    },
    DmaChannel {
        name: "DMA1_CH4",
        dma: "DMA1",
        channel: 3,
        dmamux: None,
        dmamux_channel: None,
    },
    DmaChannel {
        name: "DMA1_CH5",
        dma: "DMA1",
        channel: 4,
        dmamux: None,
        dmamux_channel: None,
    },
    DmaChannel {
        name: "DMA1_CH6",
        dma: "DMA1",
        channel: 5,
        dmamux: None,
        dmamux_channel: None,
    },
    DmaChannel {
        name: "DMA1_CH7",
        dma: "DMA1",
        channel: 6,
        dmamux: None,
        dmamux_channel: None,
    },
];
            #[path="../registers/adc_f1.rs"] pub mod adc;
#[path="../registers/afio_f1.rs"] pub mod afio;
#[path="../registers/bdma_v1.rs"] pub mod bdma;
#[path="../registers/bkp_v1.rs"] pub mod bkp;
#[path="../registers/crc_v1.rs"] pub mod crc;
#[path="../registers/dac_v2.rs"] pub mod dac;
#[path="../registers/dbgmcu_f1.rs"] pub mod dbgmcu;
#[path="../registers/exti_v1.rs"] pub mod exti;
#[path="../registers/flash_f1.rs"] pub mod flash;
#[path="../registers/gpio_v1.rs"] pub mod gpio;
#[path="../registers/i2c_v1.rs"] pub mod i2c;
#[path="../registers/iwdg_v1.rs"] pub mod iwdg;
#[path="../registers/pwr_f1.rs"] pub mod pwr;
#[path="../registers/rcc_f100.rs"] pub mod rcc;
#[path="../registers/rtc_v1.rs"] pub mod rtc;
#[path="../registers/spi_f1.rs"] pub mod spi;
#[path="../registers/timer_v1.rs"] pub mod timer;
#[path="../registers/uid_v1.rs"] pub mod uid;
#[path="../registers/usart_v1.rs"] pub mod usart;
#[path="../registers/wwdg_v1.rs"] pub mod wwdg;
