shufps/eload2/firmware/stm32-metapac/src/chips/metadata_0104.rs

                pub(crate) static PERIPHERALS: &'static [Peripheral] = &[
    Peripheral {
        name: "ADC1",
        address: 1073815552,
        registers: Some(
            PeripheralRegisters {
                kind: "adc",
                version: "v2",
                block: "ADC",
                ir: &adc::REGISTERS,
            },
        ),
        rcc: Some(
            PeripheralRcc {
                clock: "pclk2",
                enable: Some(
                    PeripheralRccRegister {
                        register: "apb2enr",
                        field: "adc1en",
                    },
                ),
                reset: None,
                mux: None,
                stop_mode: StopMode::Stop1,
            },
        ),
        pins: &[
            PeripheralPin {
                pin: "PA0",
                signal: "IN0",
                af: None,
            },
            PeripheralPin {
                pin: "PA1",
                signal: "IN1",
                af: None,
            },
            PeripheralPin {
                pin: "PA2",
                signal: "IN2",
                af: None,
            },
            PeripheralPin {
                pin: "PA3",
                signal: "IN3",
                af: None,
            },
            PeripheralPin {
                pin: "PA4",
                signal: "IN4",
                af: None,
            },
            PeripheralPin {
                pin: "PA5",
                signal: "IN5",
                af: None,
            },
            PeripheralPin {
                pin: "PA6",
                signal: "IN6",
                af: None,
            },
            PeripheralPin {
                pin: "PA7",
                signal: "IN7",
                af: None,
            },
            PeripheralPin {
                pin: "PB0",
                signal: "IN8",
                af: None,
            },
            PeripheralPin {
                pin: "PB1",
                signal: "IN9",
                af: None,
            },
            PeripheralPin {
                pin: "PC0",
                signal: "IN10",
                af: None,
            },
            PeripheralPin {
                pin: "PC1",
                signal: "IN11",
                af: None,
            },
            PeripheralPin {
                pin: "PC2",
                signal: "IN12",
                af: None,
            },
            PeripheralPin {
                pin: "PC3",
                signal: "IN13",
                af: None,
            },
            PeripheralPin {
                pin: "PC4",
                signal: "IN14",
                af: None,
            },
            PeripheralPin {
                pin: "PC5",
                signal: "IN15",
                af: None,
            },
        ],
        dma_channels: &[
            PeripheralDmaChannel {
                signal: "ADC1",
                channel: Some(
                    "DMA2_CH0",
                ),
                dmamux: None,
                dma: None,
                request: Some(
                    0,
                ),
            },
            PeripheralDmaChannel {
                signal: "ADC1",
                channel: Some(
                    "DMA2_CH4",
                ),
                dmamux: None,
                dma: None,
                request: Some(
                    0,
                ),
            },
        ],
        interrupts: &[
            PeripheralInterrupt {
                signal: "GLOBAL",
                interrupt: "ADC",
            },
        ],
    },
    Peripheral {
        name: "ADC2",
        address: 1073815808,
        registers: Some(
            PeripheralRegisters {
                kind: "adc",
                version: "v2",
                block: "ADC",
                ir: &adc::REGISTERS,
            },
        ),
        rcc: Some(
            PeripheralRcc {
                clock: "pclk2",
                enable: Some(
                    PeripheralRccRegister {
                        register: "apb2enr",
                        field: "adc2en",
                    },
                ),
                reset: None,
                mux: None,
                stop_mode: StopMode::Stop1,
            },
        ),
        pins: &[
            PeripheralPin {
                pin: "PA0",
                signal: "IN0",
                af: None,
            },
            PeripheralPin {
                pin: "PA1",
                signal: "IN1",
                af: None,
            },
            PeripheralPin {
                pin: "PA2",
                signal: "IN2",
                af: None,
            },
            PeripheralPin {
                pin: "PA3",
                signal: "IN3",
                af: None,
            },
            PeripheralPin {
                pin: "PA4",
                signal: "IN4",
                af: None,
            },
            PeripheralPin {
                pin: "PA5",
                signal: "IN5",
                af: None,
            },
            PeripheralPin {
                pin: "PA6",
                signal: "IN6",
                af: None,
            },
            PeripheralPin {
                pin: "PA7",
                signal: "IN7",
                af: None,
            },
            PeripheralPin {
                pin: "PB0",
                signal: "IN8",
                af: None,
            },
            PeripheralPin {
                pin: "PB1",
                signal: "IN9",
                af: None,
            },
            PeripheralPin {
                pin: "PC0",
                signal: "IN10",
                af: None,
            },
            PeripheralPin {
                pin: "PC1",
                signal: "IN11",
                af: None,
            },
            PeripheralPin {
                pin: "PC2",
                signal: "IN12",
                af: None,
            },
            PeripheralPin {
                pin: "PC3",
                signal: "IN13",
                af: None,
            },
            PeripheralPin {
                pin: "PC4",
                signal: "IN14",
                af: None,
            },
            PeripheralPin {
                pin: "PC5",
                signal: "IN15",
                af: None,
            },
        ],
        dma_channels: &[
            PeripheralDmaChannel {
                signal: "ADC2",
                channel: Some(
                    "DMA2_CH2",
                ),
                dmamux: None,
                dma: None,
                request: Some(
                    1,
                ),
            },
            PeripheralDmaChannel {
                signal: "ADC2",
                channel: Some(
                    "DMA2_CH3",
                ),
                dmamux: None,
                dma: None,
                request: Some(
                    1,
                ),
            },
        ],
        interrupts: &[
            PeripheralInterrupt {
                signal: "GLOBAL",
                interrupt: "ADC",
            },
        ],
    },
    Peripheral {
        name: "ADC3",
        address: 1073816064,
        registers: Some(
            PeripheralRegisters {
                kind: "adc",
                version: "v2",
                block: "ADC",
                ir: &adc::REGISTERS,
            },
        ),
        rcc: Some(
            PeripheralRcc {
                clock: "pclk2",
                enable: Some(
                    PeripheralRccRegister {
                        register: "apb2enr",
                        field: "adc3en",
                    },
                ),
                reset: None,
                mux: None,
                stop_mode: StopMode::Stop1,
            },
        ),
        pins: &[
            PeripheralPin {
                pin: "PA0",
                signal: "IN0",
                af: None,
            },
            PeripheralPin {
                pin: "PA1",
                signal: "IN1",
                af: None,
            },
            PeripheralPin {
                pin: "PA2",
                signal: "IN2",
                af: None,
            },
            PeripheralPin {
                pin: "PA3",
                signal: "IN3",
                af: None,
            },
            PeripheralPin {
                pin: "PC0",
                signal: "IN10",
                af: None,
            },
            PeripheralPin {
                pin: "PC1",
                signal: "IN11",
                af: None,
            },
            PeripheralPin {
                pin: "PC2",
                signal: "IN12",
                af: None,
            },
            PeripheralPin {
                pin: "PC3",
                signal: "IN13",
                af: None,
            },
        ],
        dma_channels: &[
            PeripheralDmaChannel {
                signal: "ADC3",
                channel: Some(
                    "DMA2_CH0",
                ),
                dmamux: None,
                dma: None,
                request: Some(
                    2,
                ),
            },
            PeripheralDmaChannel {
                signal: "ADC3",
                channel: Some(
                    "DMA2_CH1",
                ),
                dmamux: None,
                dma: None,
                request: Some(
                    2,
                ),
            },
        ],
        interrupts: &[
            PeripheralInterrupt {
                signal: "GLOBAL",
                interrupt: "ADC",
            },
        ],
    },
    Peripheral {
        name: "ADC_COMMON",
        address: 1073816320,
        registers: Some(
            PeripheralRegisters {
                kind: "adccommon",
                version: "v2",
                block: "ADC_COMMON",
                ir: &adccommon::REGISTERS,
            },
        ),
        rcc: None,
        pins: &[],
        dma_channels: &[],
        interrupts: &[],
    },
    Peripheral {
        name: "CAN1",
        address: 1073767424,
        registers: Some(
            PeripheralRegisters {
                kind: "can",
                version: "bxcan",
                block: "CAN",
                ir: &can::REGISTERS,
            },
        ),
        rcc: Some(
            PeripheralRcc {
                clock: "pclk1",
                enable: Some(
                    PeripheralRccRegister {
                        register: "apb1enr",
                        field: "can1en",
                    },
                ),
                reset: Some(
                    PeripheralRccRegister {
                        register: "apb1rstr",
                        field: "can1rst",
                    },
                ),
                mux: None,
                stop_mode: StopMode::Stop1,
            },
        ),
        pins: &[
            PeripheralPin {
                pin: "PA11",
                signal: "RX",
                af: Some(
                    9,
                ),
            },
            PeripheralPin {
                pin: "PA12",
                signal: "TX",
                af: Some(
                    9,
                ),
            },
            PeripheralPin {
                pin: "PB8",
                signal: "RX",
                af: Some(
                    9,
                ),
            },
            PeripheralPin {
                pin: "PB9",
                signal: "TX",
                af: Some(
                    9,
                ),
            },
        ],
        dma_channels: &[],
        interrupts: &[
            PeripheralInterrupt {
                signal: "RX0",
                interrupt: "CAN1_RX0",
            },
            PeripheralInterrupt {
                signal: "RX1",
                interrupt: "CAN1_RX1",
            },
            PeripheralInterrupt {
                signal: "SCE",
                interrupt: "CAN1_SCE",
            },
            PeripheralInterrupt {
                signal: "TX",
                interrupt: "CAN1_TX",
            },
        ],
    },
    Peripheral {
        name: "CAN2",
        address: 1073768448,
        registers: Some(
            PeripheralRegisters {
                kind: "can",
                version: "bxcan",
                block: "CAN",
                ir: &can::REGISTERS,
            },
        ),
        rcc: Some(
            PeripheralRcc {
                clock: "pclk1",
                enable: Some(
                    PeripheralRccRegister {
                        register: "apb1enr",
                        field: "can2en",
                    },
                ),
                reset: Some(
                    PeripheralRccRegister {
                        register: "apb1rstr",
                        field: "can2rst",
                    },
                ),
                mux: None,
                stop_mode: StopMode::Stop1,
            },
        ),
        pins: &[
            PeripheralPin {
                pin: "PB12",
                signal: "RX",
                af: Some(
                    9,
                ),
            },
            PeripheralPin {
                pin: "PB13",
                signal: "TX",
                af: Some(
                    9,
                ),
            },
            PeripheralPin {
                pin: "PB5",
                signal: "RX",
                af: Some(
                    9,
                ),
            },
            PeripheralPin {
                pin: "PB6",
                signal: "TX",
                af: Some(
                    9,
                ),
            },
        ],
        dma_channels: &[],
        interrupts: &[
            PeripheralInterrupt {
                signal: "RX0",
                interrupt: "CAN2_RX0",
            },
            PeripheralInterrupt {
                signal: "RX1",
                interrupt: "CAN2_RX1",
            },
            PeripheralInterrupt {
                signal: "SCE",
                interrupt: "CAN2_SCE",
            },
            PeripheralInterrupt {
                signal: "TX",
                interrupt: "CAN2_TX",
            },
        ],
    },
    Peripheral {
        name: "CRC",
        address: 1073885184,
        registers: Some(
            PeripheralRegisters {
                kind: "crc",
                version: "v1",
                block: "CRC",
                ir: &crc::REGISTERS,
            },
        ),
        rcc: Some(
            PeripheralRcc {
                clock: "hclk1",
                enable: Some(
                    PeripheralRccRegister {
                        register: "ahb1enr",
                        field: "crcen",
                    },
                ),
                reset: Some(
                    PeripheralRccRegister {
                        register: "ahb1rstr",
                        field: "crcrst",
                    },
                ),
                mux: None,
                stop_mode: StopMode::Stop1,
            },
        ),
        pins: &[],
        dma_channels: &[],
        interrupts: &[],
    },
    Peripheral {
        name: "DAC",
        address: 1073771520,
        registers: Some(
            PeripheralRegisters {
                kind: "dac",
                version: "v2",
                block: "DAC",
                ir: &dac::REGISTERS,
            },
        ),
        rcc: Some(
            PeripheralRcc {
                clock: "pclk1",
                enable: Some(
                    PeripheralRccRegister {
                        register: "apb1enr",
                        field: "dacen",
                    },
                ),
                reset: Some(
                    PeripheralRccRegister {
                        register: "apb1rstr",
                        field: "dacrst",
                    },
                ),
                mux: None,
                stop_mode: StopMode::Stop1,
            },
        ),
        pins: &[
            PeripheralPin {
                pin: "PA4",
                signal: "OUT1",
                af: None,
            },
            PeripheralPin {
                pin: "PA5",
                signal: "OUT2",
                af: None,
            },
        ],
        dma_channels: &[
            PeripheralDmaChannel {
                signal: "CH1",
                channel: Some(
                    "DMA1_CH5",
                ),
                dmamux: None,
                dma: None,
                request: Some(
                    7,
                ),
            },
            PeripheralDmaChannel {
                signal: "CH2",
                channel: Some(
                    "DMA1_CH6",
                ),
                dmamux: None,
                dma: None,
                request: Some(
                    7,
                ),
            },
        ],
        interrupts: &[
            PeripheralInterrupt {
                signal: "GLOBAL",
                interrupt: "TIM6_DAC",
            },
        ],
    },
    Peripheral {
        name: "DBGMCU",
        address: 3758366720,
        registers: Some(
            PeripheralRegisters {
                kind: "dbgmcu",
                version: "f2",
                block: "DBGMCU",
                ir: &dbgmcu::REGISTERS,
            },
        ),
        rcc: None,
        pins: &[],
        dma_channels: &[],
        interrupts: &[],
    },
    Peripheral {
        name: "DMA1",
        address: 1073897472,
        registers: Some(
            PeripheralRegisters {
                kind: "dma",
                version: "v2",
                block: "DMA",
                ir: &dma::REGISTERS,
            },
        ),
        rcc: Some(
            PeripheralRcc {
                clock: "hclk1",
                enable: Some(
                    PeripheralRccRegister {
                        register: "ahb1enr",
                        field: "dma1en",
                    },
                ),
                reset: Some(
                    PeripheralRccRegister {
                        register: "ahb1rstr",
                        field: "dma1rst",
                    },
                ),
                mux: None,
                stop_mode: StopMode::Stop1,
            },
        ),
        pins: &[],
        dma_channels: &[],
        interrupts: &[
            PeripheralInterrupt {
                signal: "CH0",
                interrupt: "DMA1_STREAM0",
            },
            PeripheralInterrupt {
                signal: "CH1",
                interrupt: "DMA1_STREAM1",
            },
            PeripheralInterrupt {
                signal: "CH2",
                interrupt: "DMA1_STREAM2",
            },
            PeripheralInterrupt {
                signal: "CH3",
                interrupt: "DMA1_STREAM3",
            },
            PeripheralInterrupt {
                signal: "CH4",
                interrupt: "DMA1_STREAM4",
            },
            PeripheralInterrupt {
                signal: "CH5",
                interrupt: "DMA1_STREAM5",
            },
            PeripheralInterrupt {
                signal: "CH6",
                interrupt: "DMA1_STREAM6",
            },
            PeripheralInterrupt {
                signal: "CH7",
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
            PeripheralInterrupt {
                signal: "EXTI9",
                interrupt: "EXTI9_5",
            },
        ],
    },
    Peripheral {
        name: "FLASH",
        address: 1073888256,
        registers: Some(
            PeripheralRegisters {
                kind: "flash",
                version: "f2",
                block: "FLASH",
                ir: &flash::REGISTERS,
            },
        ),
        rcc: None,
        pins: &[],
        dma_channels: &[],
        interrupts: &[
            PeripheralInterrupt {
                signal: "GLOBAL",
                interrupt: "FLASH",
            },
        ],
    },
    Peripheral {
        name: "GPIOA",
        address: 1073872896,
        registers: Some(
            PeripheralRegisters {
                kind: "gpio",
                version: "v2",
                block: "GPIO",
                ir: &gpio::REGISTERS,
            },
        ),
        rcc: Some(
            PeripheralRcc {
                clock: "hclk1",
                enable: Some(
                    PeripheralRccRegister {
                        register: "ahb1enr",
                        field: "gpioaen",
                    },
                ),
                reset: Some(
                    PeripheralRccRegister {
                        register: "ahb1rstr",
                        field: "gpioarst",
                    },
                ),
                mux: None,
                stop_mode: StopMode::Stop1,
            },
        ),
        pins: &[],
        dma_channels: &[],
        interrupts: &[],
    },
    Peripheral {
        name: "GPIOB",
        address: 1073873920,
        registers: Some(
            PeripheralRegisters {
                kind: "gpio",
                version: "v2",
                block: "GPIO",
                ir: &gpio::REGISTERS,
            },
        ),
        rcc: Some(
            PeripheralRcc {
                clock: "hclk1",
                enable: Some(
                    PeripheralRccRegister {
                        register: "ahb1enr",
                        field: "gpioben",
                    },
                ),
                reset: Some(
                    PeripheralRccRegister {
                        register: "ahb1rstr",
                        field: "gpiobrst",
                    },
                ),
                mux: None,
                stop_mode: StopMode::Stop1,
            },
        ),
        pins: &[],
        dma_channels: &[],
        interrupts: &[],
    },
    Peripheral {
        name: "GPIOC",
        address: 1073874944,
        registers: Some(
            PeripheralRegisters {
                kind: "gpio",
                version: "v2",
                block: "GPIO",
                ir: &gpio::REGISTERS,
            },
        ),
        rcc: Some(
            PeripheralRcc {
                clock: "hclk1",
                enable: Some(
                    PeripheralRccRegister {
                        register: "ahb1enr",
                        field: "gpiocen",
                    },
                ),
                reset: Some(
                    PeripheralRccRegister {
                        register: "ahb1rstr",
                        field: "gpiocrst",
                    },
                ),
                mux: None,
                stop_mode: StopMode::Stop1,
            },
        ),
        pins: &[],
        dma_channels: &[],
        interrupts: &[],
    },
    Peripheral {
        name: "GPIOD",
        address: 1073875968,
        registers: Some(
            PeripheralRegisters {
                kind: "gpio",
                version: "v2",
                block: "GPIO",
                ir: &gpio::REGISTERS,
            },
        ),
        rcc: Some(
            PeripheralRcc {
                clock: "hclk1",
                enable: Some(
                    PeripheralRccRegister {
                        register: "ahb1enr",
                        field: "gpioden",
                    },
                ),
                reset: Some(
                    PeripheralRccRegister {
                        register: "ahb1rstr",
                        field: "gpiodrst",
                    },
                ),
                mux: None,
                stop_mode: StopMode::Stop1,
            },
        ),
        pins: &[],
        dma_channels: &[],
        interrupts: &[],
    },
    Peripheral {
        name: "GPIOE",
        address: 1073876992,
        registers: Some(
            PeripheralRegisters {
                kind: "gpio",
                version: "v2",
                block: "GPIO",
                ir: &gpio::REGISTERS,
            },
        ),
        rcc: Some(
            PeripheralRcc {
                clock: "hclk1",
                enable: Some(
                    PeripheralRccRegister {
                        register: "ahb1enr",
                        field: "gpioeen",
                    },
                ),
                reset: Some(
                    PeripheralRccRegister {
                        register: "ahb1rstr",
                        field: "gpioerst",
                    },
                ),
                mux: None,
                stop_mode: StopMode::Stop1,
            },
        ),
        pins: &[],
        dma_channels: &[],
        interrupts: &[],
    },
    Peripheral {
        name: "GPIOF",
        address: 1073878016,
        registers: Some(
            PeripheralRegisters {
                kind: "gpio",
                version: "v2",
                block: "GPIO",
                ir: &gpio::REGISTERS,
            },
        ),
        rcc: Some(
            PeripheralRcc {
                clock: "hclk1",
                enable: Some(
                    PeripheralRccRegister {
                        register: "ahb1enr",
                        field: "gpiofen",
                    },
                ),
                reset: Some(
                    PeripheralRccRegister {
                        register: "ahb1rstr",
                        field: "gpiofrst",
                    },
                ),
                mux: None,
                stop_mode: StopMode::Stop1,
            },
        ),
        pins: &[],
        dma_channels: &[],
        interrupts: &[],
    },
    Peripheral {
        name: "GPIOG",
        address: 1073879040,
        registers: Some(
            PeripheralRegisters {
                kind: "gpio",
                version: "v2",
                block: "GPIO",
                ir: &gpio::REGISTERS,
            },
        ),
        rcc: Some(
            PeripheralRcc {
                clock: "hclk1",
                enable: Some(
                    PeripheralRccRegister {
                        register: "ahb1enr",
                        field: "gpiogen",
                    },
                ),
                reset: Some(
                    PeripheralRccRegister {
                        register: "ahb1rstr",
                        field: "gpiogrst",
                    },
                ),
                mux: None,
                stop_mode: StopMode::Stop1,
            },
        ),
        pins: &[],
        dma_channels: &[],
        interrupts: &[],
    },
    Peripheral {
        name: "GPIOH",
        address: 1073880064,
        registers: Some(
            PeripheralRegisters {
                kind: "gpio",
                version: "v2",
                block: "GPIO",
                ir: &gpio::REGISTERS,
            },
        ),
        rcc: Some(
            PeripheralRcc {
                clock: "hclk1",
                enable: Some(
                    PeripheralRccRegister {
                        register: "ahb1enr",
                        field: "gpiohen",
                    },
                ),
                reset: Some(
                    PeripheralRccRegister {
                        register: "ahb1rstr",
                        field: "gpiohrst",
                    },
                ),
                mux: None,
                stop_mode: StopMode::Stop1,
            },
        ),
        pins: &[],
        dma_channels: &[],
        interrupts: &[],
    },
    Peripheral {
        name: "GPIOI",
        address: 1073881088,
        registers: Some(
            PeripheralRegisters {
                kind: "gpio",
                version: "v2",
                block: "GPIO",
                ir: &gpio::REGISTERS,
            },
        ),
        rcc: Some(
            PeripheralRcc {
                clock: "hclk1",
                enable: Some(
                    PeripheralRccRegister {
                        register: "ahb1enr",
                        field: "gpioien",
                    },
                ),
                reset: Some(
                    PeripheralRccRegister {
                        register: "ahb1rstr",
                        field: "gpioirst",
                    },
                ),
                mux: None,
                stop_mode: StopMode::Stop1,
            },
        ),
        pins: &[],
        dma_channels: &[],
        interrupts: &[],
    },
    Peripheral {
        name: "I2C1",
        address: 1073763328,
        registers: Some(
            PeripheralRegisters {
                kind: "i2c",
                version: "v1",
                block: "I2C",
                ir: &i2c::REGISTERS,
            },
        ),
        rcc: Some(
            PeripheralRcc {
                clock: "pclk1",
                enable: Some(
                    PeripheralRccRegister {
                        register: "apb1enr",
                        field: "i2c1en",
                    },
                ),
                reset: Some(
                    PeripheralRccRegister {
                        register: "apb1rstr",
                        field: "i2c1rst",
                    },
                ),
                mux: None,
                stop_mode: StopMode::Stop1,
            },
        ),
        pins: &[
            PeripheralPin {
                pin: "PB5",
                signal: "SMBA",
                af: Some(
                    4,
                ),
            },
            PeripheralPin {
                pin: "PB6",
                signal: "SCL",
                af: Some(
                    4,
                ),
            },
            PeripheralPin {
                pin: "PB7",
                signal: "SDA",
                af: Some(
                    4,
                ),
            },
            PeripheralPin {
                pin: "PB8",
                signal: "SCL",
                af: Some(
                    4,
                ),
            },
            PeripheralPin {
                pin: "PB9",
                signal: "SDA",
                af: Some(
                    4,
                ),
            },
        ],
        dma_channels: &[
            PeripheralDmaChannel {
                signal: "RX",
                channel: Some(
                    "DMA1_CH0",
                ),
                dmamux: None,
                dma: None,
                request: Some(
                    1,
                ),
            },
            PeripheralDmaChannel {
                signal: "RX",
                channel: Some(
                    "DMA1_CH5",
                ),
                dmamux: None,
                dma: None,
                request: Some(
                    1,
                ),
            },
            PeripheralDmaChannel {
                signal: "TX",
                channel: Some(
                    "DMA1_CH6",
                ),
                dmamux: None,
                dma: None,
                request: Some(
                    1,
                ),
            },
            PeripheralDmaChannel {
                signal: "TX",
                channel: Some(
                    "DMA1_CH7",
                ),
                dmamux: None,
                dma: None,
                request: Some(
                    1,
                ),
            },
        ],
        interrupts: &[
            PeripheralInterrupt {
                signal: "ER",
                interrupt: "I2C1_ER",
            },
            PeripheralInterrupt {
                signal: "EV",
                interrupt: "I2C1_EV",
            },
        ],
    },
    Peripheral {
        name: "I2C2",
        address: 1073764352,
        registers: Some(
            PeripheralRegisters {
                kind: "i2c",
                version: "v1",
                block: "I2C",
                ir: &i2c::REGISTERS,
            },
        ),
        rcc: Some(
            PeripheralRcc {
                clock: "pclk1",
                enable: Some(
                    PeripheralRccRegister {
                        register: "apb1enr",
                        field: "i2c2en",
                    },
                ),
                reset: Some(
                    PeripheralRccRegister {
                        register: "apb1rstr",
                        field: "i2c2rst",
                    },
                ),
                mux: None,
                stop_mode: StopMode::Stop1,
            },
        ),
        pins: &[
            PeripheralPin {
                pin: "PB10",
                signal: "SCL",
                af: Some(
                    4,
                ),
            },
            PeripheralPin {
                pin: "PB11",
                signal: "SDA",
                af: Some(
                    4,
                ),
            },
            PeripheralPin {
                pin: "PB12",
                signal: "SMBA",
                af: Some(
                    4,
                ),
            },
        ],
        dma_channels: &[
            PeripheralDmaChannel {
                signal: "RX",
                channel: Some(
                    "DMA1_CH2",
                ),
                dmamux: None,
                dma: None,
                request: Some(
                    7,
                ),
            },
            PeripheralDmaChannel {
                signal: "RX",
                channel: Some(
                    "DMA1_CH3",
                ),
                dmamux: None,
                dma: None,
                request: Some(
                    7,
                ),
            },
            PeripheralDmaChannel {
                signal: "TX",
                channel: Some(
                    "DMA1_CH7",
                ),
                dmamux: None,
                dma: None,
                request: Some(
                    7,
                ),
            },
        ],
        interrupts: &[
            PeripheralInterrupt {
                signal: "ER",
                interrupt: "I2C2_ER",
            },
            PeripheralInterrupt {
                signal: "EV",
                interrupt: "I2C2_EV",
            },
        ],
    },
    Peripheral {
        name: "I2C3",
        address: 1073765376,
        registers: Some(
            PeripheralRegisters {
                kind: "i2c",
                version: "v1",
                block: "I2C",
                ir: &i2c::REGISTERS,
            },
        ),
        rcc: Some(
            PeripheralRcc {
                clock: "pclk1",
                enable: Some(
                    PeripheralRccRegister {
                        register: "apb1enr",
                        field: "i2c3en",
                    },
                ),
                reset: Some(
                    PeripheralRccRegister {
                        register: "apb1rstr",
                        field: "i2c3rst",
                    },
                ),
                mux: None,
                stop_mode: StopMode::Stop1,
            },
        ),
        pins: &[
            PeripheralPin {
                pin: "PA8",
                signal: "SCL",
                af: Some(
                    4,
                ),
            },
            PeripheralPin {
                pin: "PA9",
                signal: "SMBA",
                af: Some(
                    4,
                ),
            },
            PeripheralPin {
                pin: "PC9",
                signal: "SDA",
                af: Some(
                    4,
                ),
            },
        ],
        dma_channels: &[
            PeripheralDmaChannel {
                signal: "RX",
                channel: Some(
                    "DMA1_CH2",
                ),
                dmamux: None,
                dma: None,
                request: Some(
                    3,
                ),
            },
            PeripheralDmaChannel {
                signal: "TX",
                channel: Some(
                    "DMA1_CH4",
                ),
                dmamux: None,
                dma: None,
                request: Some(
                    3,
                ),
            },
        ],
        interrupts: &[
            PeripheralInterrupt {
                signal: "ER",
                interrupt: "I2C3_ER",
            },
            PeripheralInterrupt {
                signal: "EV",
                interrupt: "I2C3_EV",
            },
        ],
    },
    Peripheral {
        name: "IWDG",
        address: 1073754112,
        registers: Some(
            PeripheralRegisters {
                kind: "iwdg",
                version: "v1",
                block: "IWDG",
                ir: &iwdg::REGISTERS,
            },
        ),
        rcc: None,
        pins: &[],
        dma_channels: &[],
        interrupts: &[],
    },
    Peripheral {
        name: "PWR",
        address: 1073770496,
        registers: Some(
            PeripheralRegisters {
                kind: "pwr",
                version: "f2",
                block: "PWR",
                ir: &pwr::REGISTERS,
            },
        ),
        rcc: Some(
            PeripheralRcc {
                clock: "pclk1",
                enable: Some(
                    PeripheralRccRegister {
                        register: "apb1enr",
                        field: "pwren",
                    },
                ),
                reset: Some(
                    PeripheralRccRegister {
                        register: "apb1rstr",
                        field: "pwrrst",
                    },
                ),
                mux: None,
                stop_mode: StopMode::Stop1,
            },
        ),
        pins: &[],
        dma_channels: &[],
        interrupts: &[],
    },
    Peripheral {
        name: "RCC",
        address: 1073887232,
        registers: Some(
            PeripheralRegisters {
                kind: "rcc",
                version: "f2",
                block: "RCC",
                ir: &rcc::REGISTERS,
            },
        ),
        rcc: None,
        pins: &[
            PeripheralPin {
                pin: "PA8",
                signal: "MCO_1",
                af: Some(
                    0,
                ),
            },
            PeripheralPin {
                pin: "PC14",
                signal: "OSC32_IN",
                af: Some(
                    0,
                ),
            },
            PeripheralPin {
                pin: "PC15",
                signal: "OSC32_OUT",
                af: Some(
                    0,
                ),
            },
            PeripheralPin {
                pin: "PC9",
                signal: "MCO_2",
                af: Some(
                    0,
                ),
            },
            PeripheralPin {
                pin: "PH0",
                signal: "OSC_IN",
                af: Some(
                    0,
                ),
            },
            PeripheralPin {
                pin: "PH1",
                signal: "OSC_OUT",
                af: Some(
                    0,
                ),
            },
        ],
        dma_channels: &[],
        interrupts: &[
            PeripheralInterrupt {
                signal: "GLOBAL",
                interrupt: "RCC",
            },
        ],
    },
    Peripheral {
        name: "RNG",
        address: 1342572544,
        registers: Some(
            PeripheralRegisters {
                kind: "rng",
                version: "v1",
                block: "RNG",
                ir: &rng::REGISTERS,
            },
        ),
        rcc: Some(
            PeripheralRcc {
                clock: "hclk2",
                enable: Some(
                    PeripheralRccRegister {
                        register: "ahb2enr",
                        field: "rngen",
                    },
                ),
                reset: Some(
                    PeripheralRccRegister {
                        register: "ahb2rstr",
                        field: "rngrst",
                    },
                ),
                mux: None,
                stop_mode: StopMode::Stop1,
            },
        ),
        pins: &[],
        dma_channels: &[],
        interrupts: &[
            PeripheralInterrupt {
                signal: "GLOBAL",
                interrupt: "RNG",
            },
        ],
    },
    Peripheral {
        name: "RTC",
        address: 1073752064,
        registers: Some(
            PeripheralRegisters {
                kind: "rtc",
                version: "v2f2",
                block: "RTC",
                ir: &rtc::REGISTERS,
            },
        ),
        rcc: None,
        pins: &[
            PeripheralPin {
                pin: "PB15",
                signal: "REFIN",
                af: Some(
                    0,
                ),
            },
            PeripheralPin {
                pin: "PC13",
                signal: "AF1",
                af: Some(
                    0,
                ),
            },
        ],
        dma_channels: &[],
        interrupts: &[
            PeripheralInterrupt {
                signal: "ALARM",
                interrupt: "RTC_ALARM",
            },
            PeripheralInterrupt {
                signal: "STAMP",
                interrupt: "TAMP_STAMP",
            },
            PeripheralInterrupt {
                signal: "TAMP",
                interrupt: "TAMP_STAMP",
            },
            PeripheralInterrupt {
                signal: "WKUP",
                interrupt: "RTC_WKUP",
            },
        ],
    },
    Peripheral {
        name: "SDIO",
        address: 1073818624,
        registers: Some(
            PeripheralRegisters {
                kind: "sdmmc",
                version: "v1",
                block: "SDMMC",
                ir: &sdmmc::REGISTERS,
            },
        ),
        rcc: Some(
            PeripheralRcc {
                clock: "pclk2",
                enable: Some(
                    PeripheralRccRegister {
                        register: "apb2enr",
                        field: "sdioen",
                    },
                ),
                reset: Some(
                    PeripheralRccRegister {
                        register: "apb2rstr",
                        field: "sdiorst",
                    },
                ),
                mux: None,
                stop_mode: StopMode::Stop1,
            },
        ),
        pins: &[
            PeripheralPin {
                pin: "PB8",
                signal: "D4",
                af: Some(
                    12,
                ),
            },
            PeripheralPin {
                pin: "PB9",
                signal: "D5",
                af: Some(
                    12,
                ),
            },
            PeripheralPin {
                pin: "PC10",
                signal: "D2",
                af: Some(
                    12,
                ),
            },
            PeripheralPin {
                pin: "PC11",
                signal: "D3",
                af: Some(
                    12,
                ),
            },
            PeripheralPin {
                pin: "PC12",
                signal: "CK",
                af: Some(
                    12,
                ),
            },
            PeripheralPin {
                pin: "PC6",
                signal: "D6",
                af: Some(
                    12,
                ),
            },
            PeripheralPin {
                pin: "PC7",
                signal: "D7",
                af: Some(
                    12,
                ),
            },
            PeripheralPin {
                pin: "PC8",
                signal: "D0",
                af: Some(
                    12,
                ),
            },
            PeripheralPin {
                pin: "PC9",
                signal: "D1",
                af: Some(
                    12,
                ),
            },
            PeripheralPin {
                pin: "PD2",
                signal: "CMD",
                af: Some(
                    12,
                ),
            },
        ],
        dma_channels: &[
            PeripheralDmaChannel {
                signal: "SDIO",
                channel: Some(
                    "DMA2_CH3",
                ),
                dmamux: None,
                dma: None,
                request: Some(
                    4,
                ),
            },
            PeripheralDmaChannel {
                signal: "RX",
                channel: Some(
                    "DMA2_CH3",
                ),
                dmamux: None,
                dma: None,
                request: Some(
                    4,
                ),
            },
            PeripheralDmaChannel {
                signal: "TX",
                channel: Some(
                    "DMA2_CH3",
                ),
                dmamux: None,
                dma: None,
                request: Some(
                    4,
                ),
            },
            PeripheralDmaChannel {
                signal: "SDIO",
                channel: Some(
                    "DMA2_CH6",
                ),
                dmamux: None,
                dma: None,
                request: Some(
                    4,
                ),
            },
            PeripheralDmaChannel {
                signal: "RX",
                channel: Some(
                    "DMA2_CH6",
                ),
                dmamux: None,
                dma: None,
                request: Some(
                    4,
                ),
            },
            PeripheralDmaChannel {
                signal: "TX",
                channel: Some(
                    "DMA2_CH6",
                ),
                dmamux: None,
                dma: None,
                request: Some(
                    4,
                ),
            },
        ],
        interrupts: &[
            PeripheralInterrupt {
                signal: "GLOBAL",
                interrupt: "SDIO",
            },
        ],
    },
    Peripheral {
        name: "SPI1",
        address: 1073819648,
        registers: Some(
            PeripheralRegisters {
                kind: "spi",
                version: "v1",
                block: "SPI",
                ir: &spi::REGISTERS,
            },
        ),
        rcc: Some(
            PeripheralRcc {
                clock: "pclk2",
                enable: Some(
                    PeripheralRccRegister {
                        register: "apb2enr",
                        field: "spi1en",
                    },
                ),
                reset: Some(
                    PeripheralRccRegister {
                        register: "apb2rstr",
                        field: "spi1rst",
                    },
                ),
                mux: None,
                stop_mode: StopMode::Stop1,
            },
        ),
        pins: &[
            PeripheralPin {
                pin: "PA15",
                signal: "NSS",
                af: Some(
                    5,
                ),
            },
            PeripheralPin {
                pin: "PA4",
                signal: "NSS",
                af: Some(
                    5,
                ),
            },
            PeripheralPin {
                pin: "PA5",
                signal: "SCK",
                af: Some(
                    5,
                ),
            },
            PeripheralPin {
                pin: "PA6",
                signal: "MISO",
                af: Some(
                    5,
                ),
            },
            PeripheralPin {
                pin: "PA7",
                signal: "MOSI",
                af: Some(
                    5,
                ),
            },
            PeripheralPin {
                pin: "PB3",
                signal: "SCK",
                af: Some(
                    5,
                ),
            },
            PeripheralPin {
                pin: "PB4",
                signal: "MISO",
                af: Some(
                    5,
                ),
            },
            PeripheralPin {
                pin: "PB5",
                signal: "MOSI",
                af: Some(
                    5,
                ),
            },
        ],
        dma_channels: &[
            PeripheralDmaChannel {
                signal: "RX",
                channel: Some(
                    "DMA2_CH0",
                ),
                dmamux: None,
                dma: None,
                request: Some(
                    3,
                ),
            },
            PeripheralDmaChannel {
                signal: "RX",
                channel: Some(
                    "DMA2_CH2",
                ),
                dmamux: None,
                dma: None,
                request: Some(
                    3,
                ),
            },
            PeripheralDmaChannel {
                signal: "TX",
                channel: Some(
                    "DMA2_CH3",
                ),
                dmamux: None,
                dma: None,
                request: Some(
                    3,
                ),
            },
            PeripheralDmaChannel {
                signal: "TX",
                channel: Some(
                    "DMA2_CH5",
                ),
                dmamux: None,
                dma: None,
                request: Some(
                    3,
                ),
            },
        ],
        interrupts: &[
            PeripheralInterrupt {
                signal: "GLOBAL",
                interrupt: "SPI1",
            },
        ],
    },
    Peripheral {
        name: "SPI2",
        address: 1073756160,
        registers: Some(
            PeripheralRegisters {
                kind: "spi",
                version: "v1",
                block: "SPI",
                ir: &spi::REGISTERS,
            },
        ),
        rcc: Some(
            PeripheralRcc {
                clock: "pclk1",
                enable: Some(
                    PeripheralRccRegister {
                        register: "apb1enr",
                        field: "spi2en",
                    },
                ),
                reset: Some(
                    PeripheralRccRegister {
                        register: "apb1rstr",
                        field: "spi2rst",
                    },
                ),
                mux: None,
                stop_mode: StopMode::Stop1,
            },
        ),
        pins: &[
            PeripheralPin {
                pin: "PB10",
                signal: "I2S_SCK",
                af: Some(
                    5,
                ),
            },
            PeripheralPin {
                pin: "PB10",
                signal: "SCK",
                af: Some(
                    5,
                ),
            },
            PeripheralPin {
                pin: "PB12",
                signal: "I2S_WS",
                af: Some(
                    5,
                ),
            },
            PeripheralPin {
                pin: "PB12",
                signal: "NSS",
                af: Some(
                    5,
                ),
            },
            PeripheralPin {
                pin: "PB13",
                signal: "I2S_SCK",
                af: Some(
                    5,
                ),
            },
            PeripheralPin {
                pin: "PB13",
                signal: "SCK",
                af: Some(
                    5,
                ),
            },
            PeripheralPin {
                pin: "PB14",
                signal: "MISO",
                af: Some(
                    5,
                ),
            },
            PeripheralPin {
                pin: "PB15",
                signal: "I2S_SD",
                af: Some(
                    5,
                ),
            },
            PeripheralPin {
                pin: "PB15",
                signal: "MOSI",
                af: Some(
                    5,
                ),
            },
            PeripheralPin {
                pin: "PB9",
                signal: "I2S_WS",
                af: Some(
                    5,
                ),
            },
            PeripheralPin {
                pin: "PB9",
                signal: "NSS",
                af: Some(
                    5,
                ),
            },
            PeripheralPin {
                pin: "PC2",
                signal: "MISO",
                af: Some(
                    5,
                ),
            },
            PeripheralPin {
                pin: "PC3",
                signal: "I2S_SD",
                af: Some(
                    5,
                ),
            },
            PeripheralPin {
                pin: "PC3",
                signal: "MOSI",
                af: Some(
                    5,
                ),
            },
            PeripheralPin {
                pin: "PC6",
                signal: "I2S_MCK",
                af: Some(
                    5,
                ),
            },
        ],
        dma_channels: &[
            PeripheralDmaChannel {
                signal: "RX",
                channel: Some(
                    "DMA1_CH3",
                ),
                dmamux: None,
                dma: None,
                request: Some(
                    0,
                ),
            },
            PeripheralDmaChannel {
                signal: "TX",
                channel: Some(
                    "DMA1_CH4",
                ),
                dmamux: None,
                dma: None,
                request: Some(
                    0,
                ),
            },
        ],
        interrupts: &[
            PeripheralInterrupt {
                signal: "GLOBAL",
                interrupt: "SPI2",
            },
        ],
    },
    Peripheral {
        name: "SPI3",
        address: 1073757184,
        registers: Some(
            PeripheralRegisters {
                kind: "spi",
                version: "v1",
                block: "SPI",
                ir: &spi::REGISTERS,
            },
        ),
        rcc: Some(
            PeripheralRcc {
                clock: "pclk1",
                enable: Some(
                    PeripheralRccRegister {
                        register: "apb1enr",
                        field: "spi3en",
                    },
                ),
                reset: Some(
                    PeripheralRccRegister {
                        register: "apb1rstr",
                        field: "spi3rst",
                    },
                ),
                mux: None,
                stop_mode: StopMode::Stop1,
            },
        ),
        pins: &[
            PeripheralPin {
                pin: "PA15",
                signal: "I2S_WS",
                af: Some(
                    6,
                ),
            },
            PeripheralPin {
                pin: "PA15",
                signal: "NSS",
                af: Some(
                    6,
                ),
            },
            PeripheralPin {
                pin: "PA4",
                signal: "I2S_WS",
                af: Some(
                    6,
                ),
            },
            PeripheralPin {
                pin: "PA4",
                signal: "NSS",
                af: Some(
                    6,
                ),
            },
            PeripheralPin {
                pin: "PB3",
                signal: "I2S_SCK",
                af: Some(
                    6,
                ),
            },
            PeripheralPin {
                pin: "PB3",
                signal: "SCK",
                af: Some(
                    6,
                ),
            },
            PeripheralPin {
                pin: "PB4",
                signal: "MISO",
                af: Some(
                    6,
                ),
            },
            PeripheralPin {
                pin: "PB5",
                signal: "I2S_SD",
                af: Some(
                    6,
                ),
            },
            PeripheralPin {
                pin: "PB5",
                signal: "MOSI",
                af: Some(
                    6,
                ),
            },
            PeripheralPin {
                pin: "PC10",
                signal: "I2S_SCK",
                af: Some(
                    6,
                ),
            },
            PeripheralPin {
                pin: "PC10",
                signal: "SCK",
                af: Some(
                    6,
                ),
            },
            PeripheralPin {
                pin: "PC11",
                signal: "MISO",
                af: Some(
                    6,
                ),
            },
            PeripheralPin {
                pin: "PC12",
                signal: "I2S_SD",
                af: Some(
                    6,
                ),
            },
            PeripheralPin {
                pin: "PC12",
                signal: "MOSI",
                af: Some(
                    6,
                ),
            },
            PeripheralPin {
                pin: "PC7",
                signal: "I2S_MCK",
                af: Some(
                    6,
                ),
            },
        ],
        dma_channels: &[
            PeripheralDmaChannel {
                signal: "RX",
                channel: Some(
                    "DMA1_CH0",
                ),
                dmamux: None,
                dma: None,
                request: Some(
                    0,
                ),
            },
            PeripheralDmaChannel {
                signal: "RX",
                channel: Some(
                    "DMA1_CH2",
                ),
                dmamux: None,
                dma: None,
                request: Some(
                    0,
                ),
            },
            PeripheralDmaChannel {
                signal: "TX",
                channel: Some(
                    "DMA1_CH5",
                ),
                dmamux: None,
                dma: None,
                request: Some(
                    0,
                ),
            },
            PeripheralDmaChannel {
                signal: "TX",
                channel: Some(
                    "DMA1_CH7",
                ),
                dmamux: None,
                dma: None,
                request: Some(
                    0,
                ),
            },
        ],
        interrupts: &[
            PeripheralInterrupt {
                signal: "GLOBAL",
                interrupt: "SPI3",
            },
        ],
    },
    Peripheral {
        name: "SYSCFG",
        address: 1073821696,
        registers: Some(
            PeripheralRegisters {
                kind: "syscfg",
                version: "f2",
                block: "SYSCFG",
                ir: &syscfg::REGISTERS,
            },
        ),
        rcc: Some(
            PeripheralRcc {
                clock: "pclk2",
                enable: Some(
                    PeripheralRccRegister {
                        register: "apb2enr",
                        field: "syscfgen",
                    },
                ),
                reset: Some(
                    PeripheralRccRegister {
                        register: "apb2rstr",
                        field: "syscfgrst",
                    },
                ),
                mux: None,
                stop_mode: StopMode::Stop1,
            },
        ),
        pins: &[],
        dma_channels: &[],
        interrupts: &[],
    },
    Peripheral {
        name: "TIM1",
        address: 1073807360,
        registers: Some(
            PeripheralRegisters {
                kind: "timer",
                version: "v1",
                block: "TIM_ADV",
                ir: &timer::REGISTERS,
            },
        ),
        rcc: Some(
            PeripheralRcc {
                clock: "pclk2_tim",
                enable: Some(
                    PeripheralRccRegister {
                        register: "apb2enr",
                        field: "tim1en",
                    },
                ),
                reset: Some(
                    PeripheralRccRegister {
                        register: "apb2rstr",
                        field: "tim1rst",
                    },
                ),
                mux: None,
                stop_mode: StopMode::Stop1,
            },
        ),
        pins: &[
            PeripheralPin {
                pin: "PA10",
                signal: "CH3",
                af: Some(
                    1,
                ),
            },
            PeripheralPin {
                pin: "PA11",
                signal: "CH4",
                af: Some(
                    1,
                ),
            },
            PeripheralPin {
                pin: "PA12",
                signal: "ETR",
                af: Some(
                    1,
                ),
            },
            PeripheralPin {
                pin: "PA6",
                signal: "BKIN",
                af: Some(
                    1,
                ),
            },
            PeripheralPin {
                pin: "PA7",
                signal: "CH1N",
                af: Some(
                    1,
                ),
            },
            PeripheralPin {
                pin: "PA8",
                signal: "CH1",
                af: Some(
                    1,
                ),
            },
            PeripheralPin {
                pin: "PA9",
                signal: "CH2",
                af: Some(
                    1,
                ),
            },
            PeripheralPin {
                pin: "PB0",
                signal: "CH2N",
                af: Some(
                    1,
                ),
            },
            PeripheralPin {
                pin: "PB1",
                signal: "CH3N",
                af: Some(
                    1,
                ),
            },
            PeripheralPin {
                pin: "PB12",
                signal: "BKIN",
                af: Some(
                    1,
                ),
            },
            PeripheralPin {
                pin: "PB13",
                signal: "CH1N",
                af: Some(
                    1,
                ),
            },
            PeripheralPin {
                pin: "PB14",
                signal: "CH2N",
                af: Some(
                    1,
                ),
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
                interrupt: "TIM1_TRG_COM_TIM11",
            },
            PeripheralInterrupt {
                signal: "UP",
                interrupt: "TIM1_UP_TIM10",
            },
        ],
    },
    Peripheral {
        name: "TIM10",
        address: 1073824768,
        registers: Some(
            PeripheralRegisters {
                kind: "timer",
                version: "v1",
                block: "TIM_GP16",
                ir: &timer::REGISTERS,
            },
        ),
        rcc: Some(
            PeripheralRcc {
                clock: "pclk2_tim",
                enable: Some(
                    PeripheralRccRegister {
                        register: "apb2enr",
                        field: "tim10en",
                    },
                ),
                reset: Some(
                    PeripheralRccRegister {
                        register: "apb2rstr",
                        field: "tim10rst",
                    },
                ),
                mux: None,
                stop_mode: StopMode::Stop1,
            },
        ),
        pins: &[
            PeripheralPin {
                pin: "PB8",
                signal: "CH1",
                af: Some(
                    3,
                ),
            },
        ],
        dma_channels: &[],
        interrupts: &[
            PeripheralInterrupt {
                signal: "BRK",
                interrupt: "TIM1_UP_TIM10",
            },
            PeripheralInterrupt {
                signal: "CC",
                interrupt: "TIM1_UP_TIM10",
            },
            PeripheralInterrupt {
                signal: "COM",
                interrupt: "TIM1_UP_TIM10",
            },
            PeripheralInterrupt {
                signal: "TRG",
                interrupt: "TIM1_UP_TIM10",
            },
            PeripheralInterrupt {
                signal: "UP",
                interrupt: "TIM1_UP_TIM10",
            },
        ],
    },
    Peripheral {
        name: "TIM11",
        address: 1073825792,
        registers: Some(
            PeripheralRegisters {
                kind: "timer",
                version: "v1",
                block: "TIM_GP16",
                ir: &timer::REGISTERS,
            },
        ),
        rcc: Some(
            PeripheralRcc {
                clock: "pclk2_tim",
                enable: Some(
                    PeripheralRccRegister {
                        register: "apb2enr",
                        field: "tim11en",
                    },
                ),
                reset: Some(
                    PeripheralRccRegister {
                        register: "apb2rstr",
                        field: "tim11rst",
                    },
                ),
                mux: None,
                stop_mode: StopMode::Stop1,
            },
        ),
        pins: &[
            PeripheralPin {
                pin: "PB9",
                signal: "CH1",
                af: Some(
                    3,
                ),
            },
        ],
        dma_channels: &[],
        interrupts: &[
            PeripheralInterrupt {
                signal: "BRK",
                interrupt: "TIM1_TRG_COM_TIM11",
            },
            PeripheralInterrupt {
                signal: "CC",
                interrupt: "TIM1_TRG_COM_TIM11",
            },
            PeripheralInterrupt {
                signal: "COM",
                interrupt: "TIM1_TRG_COM_TIM11",
            },
            PeripheralInterrupt {
                signal: "TRG",
                interrupt: "TIM1_TRG_COM_TIM11",
            },
            PeripheralInterrupt {
                signal: "UP",
                interrupt: "TIM1_TRG_COM_TIM11",
            },
        ],
    },
    Peripheral {
        name: "TIM12",
        address: 1073747968,
        registers: Some(
            PeripheralRegisters {
                kind: "timer",
                version: "v1",
                block: "TIM_GP16",
                ir: &timer::REGISTERS,
            },
        ),
        rcc: Some(
            PeripheralRcc {
                clock: "pclk1_tim",
                enable: Some(
                    PeripheralRccRegister {
                        register: "apb1enr",
                        field: "tim12en",
                    },
                ),
                reset: Some(
                    PeripheralRccRegister {
                        register: "apb1rstr",
                        field: "tim12rst",
                    },
                ),
                mux: None,
                stop_mode: StopMode::Stop1,
            },
        ),
        pins: &[
            PeripheralPin {
                pin: "PB14",
                signal: "CH1",
                af: Some(
                    9,
                ),
            },
            PeripheralPin {
                pin: "PB15",
                signal: "CH2",
                af: Some(
                    9,
                ),
            },
        ],
        dma_channels: &[],
        interrupts: &[
            PeripheralInterrupt {
                signal: "BRK",
                interrupt: "TIM8_BRK_TIM12",
            },
            PeripheralInterrupt {
                signal: "CC",
                interrupt: "TIM8_BRK_TIM12",
            },
            PeripheralInterrupt {
                signal: "COM",
                interrupt: "TIM8_BRK_TIM12",
            },
            PeripheralInterrupt {
                signal: "TRG",
                interrupt: "TIM8_BRK_TIM12",
            },
            PeripheralInterrupt {
                signal: "UP",
                interrupt: "TIM8_BRK_TIM12",
            },
        ],
    },
    Peripheral {
        name: "TIM13",
        address: 1073748992,
        registers: Some(
            PeripheralRegisters {
                kind: "timer",
                version: "v1",
                block: "TIM_GP16",
                ir: &timer::REGISTERS,
            },
        ),
        rcc: Some(
            PeripheralRcc {
                clock: "pclk1_tim",
                enable: Some(
                    PeripheralRccRegister {
                        register: "apb1enr",
                        field: "tim13en",
                    },
                ),
                reset: Some(
                    PeripheralRccRegister {
                        register: "apb1rstr",
                        field: "tim13rst",
                    },
                ),
                mux: None,
                stop_mode: StopMode::Stop1,
            },
        ),
        pins: &[
            PeripheralPin {
                pin: "PA6",
                signal: "CH1",
                af: Some(
                    9,
                ),
            },
        ],
        dma_channels: &[],
        interrupts: &[
            PeripheralInterrupt {
                signal: "BRK",
                interrupt: "TIM8_UP_TIM13",
            },
            PeripheralInterrupt {
                signal: "CC",
                interrupt: "TIM8_UP_TIM13",
            },
            PeripheralInterrupt {
                signal: "COM",
                interrupt: "TIM8_UP_TIM13",
            },
            PeripheralInterrupt {
                signal: "TRG",
                interrupt: "TIM8_UP_TIM13",
            },
            PeripheralInterrupt {
                signal: "UP",
                interrupt: "TIM8_UP_TIM13",
            },
        ],
    },
    Peripheral {
        name: "TIM14",
        address: 1073750016,
        registers: Some(
            PeripheralRegisters {
                kind: "timer",
                version: "v1",
                block: "TIM_GP16",
                ir: &timer::REGISTERS,
            },
        ),
        rcc: Some(
            PeripheralRcc {
                clock: "pclk1_tim",
                enable: Some(
                    PeripheralRccRegister {
                        register: "apb1enr",
                        field: "tim14en",
                    },
                ),
                reset: Some(
                    PeripheralRccRegister {
                        register: "apb1rstr",
                        field: "tim14rst",
                    },
                ),
                mux: None,
                stop_mode: StopMode::Stop1,
            },
        ),
        pins: &[
            PeripheralPin {
                pin: "PA7",
                signal: "CH1",
                af: Some(
                    9,
                ),
            },
        ],
        dma_channels: &[],
        interrupts: &[
            PeripheralInterrupt {
                signal: "BRK",
                interrupt: "TIM8_TRG_COM_TIM14",
            },
            PeripheralInterrupt {
                signal: "CC",
                interrupt: "TIM8_TRG_COM_TIM14",
            },
            PeripheralInterrupt {
                signal: "COM",
                interrupt: "TIM8_TRG_COM_TIM14",
            },
            PeripheralInterrupt {
                signal: "TRG",
                interrupt: "TIM8_TRG_COM_TIM14",
            },
            PeripheralInterrupt {
                signal: "UP",
                interrupt: "TIM8_TRG_COM_TIM14",
            },
        ],
    },
    Peripheral {
        name: "TIM2",
        address: 1073741824,
        registers: Some(
            PeripheralRegisters {
                kind: "timer",
                version: "v1",
                block: "TIM_GP32",
                ir: &timer::REGISTERS,
            },
        ),
        rcc: Some(
            PeripheralRcc {
                clock: "pclk1_tim",
                enable: Some(
                    PeripheralRccRegister {
                        register: "apb1enr",
                        field: "tim2en",
                    },
                ),
                reset: Some(
                    PeripheralRccRegister {
                        register: "apb1rstr",
                        field: "tim2rst",
                    },
                ),
                mux: None,
                stop_mode: StopMode::Stop1,
            },
        ),
        pins: &[
            PeripheralPin {
                pin: "PA0",
                signal: "CH1",
                af: Some(
                    1,
                ),
            },
            PeripheralPin {
                pin: "PA0",
                signal: "ETR",
                af: Some(
                    1,
                ),
            },
            PeripheralPin {
                pin: "PA1",
                signal: "CH2",
                af: Some(
                    1,
                ),
            },
            PeripheralPin {
                pin: "PA15",
                signal: "CH1",
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
                request: Some(
                    5,
                ),
            },
            PeripheralDmaChannel {
                signal: "UP",
                channel: Some(
                    "DMA1_CH2",
                ),
                dmamux: None,
                dma: None,
                request: Some(
                    5,
                ),
            },
            PeripheralDmaChannel {
                signal: "CH1",
                channel: Some(
                    "DMA1_CH4",
                ),
                dmamux: None,
                dma: None,
                request: Some(
                    5,
                ),
            },
            PeripheralDmaChannel {
                signal: "TRIG",
                channel: Some(
                    "DMA1_CH4",
                ),
                dmamux: None,
                dma: None,
                request: Some(
                    5,
                ),
            },
            PeripheralDmaChannel {
                signal: "CH2",
                channel: Some(
                    "DMA1_CH5",
                ),
                dmamux: None,
                dma: None,
                request: Some(
                    5,
                ),
            },
            PeripheralDmaChannel {
                signal: "CH3",
                channel: Some(
                    "DMA1_CH7",
                ),
                dmamux: None,
                dma: None,
                request: Some(
                    5,
                ),
            },
        ],
        interrupts: &[
            PeripheralInterrupt {
                signal: "BRK",
                interrupt: "TIM3",
            },
            PeripheralInterrupt {
                signal: "CC",
                interrupt: "TIM3",
            },
            PeripheralInterrupt {
                signal: "COM",
                interrupt: "TIM3",
            },
            PeripheralInterrupt {
                signal: "TRG",
                interrupt: "TIM3",
            },
            PeripheralInterrupt {
                signal: "UP",
                interrupt: "TIM3",
            },
        ],
    },
    Peripheral {
        name: "TIM4",
        address: 1073743872,
        registers: Some(
            PeripheralRegisters {
                kind: "timer",
                version: "v1",
                block: "TIM_GP16",
                ir: &timer::REGISTERS,
            },
        ),
        rcc: Some(
            PeripheralRcc {
                clock: "pclk1_tim",
                enable: Some(
                    PeripheralRccRegister {
                        register: "apb1enr",
                        field: "tim4en",
                    },
                ),
                reset: Some(
                    PeripheralRccRegister {
                        register: "apb1rstr",
                        field: "tim4rst",
                    },
                ),
                mux: None,
                stop_mode: StopMode::Stop1,
            },
        ),
        pins: &[
            PeripheralPin {
                pin: "PB6",
                signal: "CH1",
                af: Some(
                    2,
                ),
            },
            PeripheralPin {
                pin: "PB7",
                signal: "CH2",
                af: Some(
                    2,
                ),
            },
            PeripheralPin {
                pin: "PB8",
                signal: "CH3",
                af: Some(
                    2,
                ),
            },
            PeripheralPin {
                pin: "PB9",
                signal: "CH4",
                af: Some(
                    2,
                ),
            },
        ],
        dma_channels: &[
            PeripheralDmaChannel {
                signal: "CH1",
                channel: Some(
                    "DMA1_CH0",
                ),
                dmamux: None,
                dma: None,
                request: Some(
                    2,
                ),
            },
            PeripheralDmaChannel {
                signal: "CH2",
                channel: Some(
                    "DMA1_CH3",
                ),
                dmamux: None,
                dma: None,
                request: Some(
                    2,
                ),
            },
            PeripheralDmaChannel {
                signal: "UP",
                channel: Some(
                    "DMA1_CH6",
                ),
                dmamux: None,
                dma: None,
                request: Some(
                    2,
                ),
            },
            PeripheralDmaChannel {
                signal: "CH3",
                channel: Some(
                    "DMA1_CH7",
                ),
                dmamux: None,
                dma: None,
                request: Some(
                    2,
                ),
            },
        ],
        interrupts: &[
            PeripheralInterrupt {
                signal: "BRK",
                interrupt: "TIM4",
            },
            PeripheralInterrupt {
                signal: "CC",
                interrupt: "TIM4",
            },
            PeripheralInterrupt {
                signal: "COM",
                interrupt: "TIM4",
            },
            PeripheralInterrupt {
                signal: "TRG",
                interrupt: "TIM4",
            },
            PeripheralInterrupt {
                signal: "UP",
                interrupt: "TIM4",
            },
        ],
    },
    Peripheral {
        name: "TIM5",
        address: 1073744896,
        registers: Some(
            PeripheralRegisters {
                kind: "timer",
                version: "v1",
                block: "TIM_GP32",
                ir: &timer::REGISTERS,
            },
        ),
        rcc: Some(
            PeripheralRcc {
                clock: "pclk1_tim",
                enable: Some(
                    PeripheralRccRegister {
                        register: "apb1enr",
                        field: "tim5en",
                    },
                ),
                reset: Some(
                    PeripheralRccRegister {
                        register: "apb1rstr",
                        field: "tim5rst",
                    },
                ),
                mux: None,
                stop_mode: StopMode::Stop1,
            },
        ),
        pins: &[
            PeripheralPin {
                pin: "PA0",
                signal: "CH1",
                af: Some(
                    2,
                ),
            },
            PeripheralPin {
                pin: "PA1",
                signal: "CH2",
                af: Some(
                    2,
                ),
            },
            PeripheralPin {
                pin: "PA2",
                signal: "CH3",
                af: Some(
                    2,
                ),
            },
            PeripheralPin {
                pin: "PA3",
                signal: "CH4",
                af: Some(
                    2,
                ),
            },
        ],
        dma_channels: &[
            PeripheralDmaChannel {
                signal: "CH3",
                channel: Some(
                    "DMA1_CH0",
                ),
                dmamux: None,
                dma: None,
                request: Some(
                    6,
                ),
            },
            PeripheralDmaChannel {
                signal: "UP",
                channel: Some(
                    "DMA1_CH0",
                ),
                dmamux: None,
                dma: None,
                request: Some(
                    6,
                ),
            },
            PeripheralDmaChannel {
                signal: "CH4",
                channel: Some(
                    "DMA1_CH1",
                ),
                dmamux: None,
                dma: None,
                request: Some(
                    6,
                ),
            },
            PeripheralDmaChannel {
                signal: "TRIG",
                channel: Some(
                    "DMA1_CH1",
                ),
                dmamux: None,
                dma: None,
                request: Some(
                    6,
                ),
            },
            PeripheralDmaChannel {
                signal: "CH1",
                channel: Some(
                    "DMA1_CH2",
                ),
                dmamux: None,
                dma: None,
                request: Some(
                    6,
                ),
            },
            PeripheralDmaChannel {
                signal: "CH4",
                channel: Some(
                    "DMA1_CH3",
                ),
                dmamux: None,
                dma: None,
                request: Some(
                    6,
                ),
            },
            PeripheralDmaChannel {
                signal: "TRIG",
                channel: Some(
                    "DMA1_CH3",
                ),
                dmamux: None,
                dma: None,
                request: Some(
                    6,
                ),
            },
            PeripheralDmaChannel {
                signal: "CH2",
                channel: Some(
                    "DMA1_CH4",
                ),
                dmamux: None,
                dma: None,
                request: Some(
                    6,
                ),
            },
            PeripheralDmaChannel {
                signal: "UP",
                channel: Some(
                    "DMA1_CH6",
                ),
                dmamux: None,
                dma: None,
                request: Some(
                    6,
                ),
            },
        ],
        interrupts: &[
            PeripheralInterrupt {
                signal: "BRK",
                interrupt: "TIM5",
            },
            PeripheralInterrupt {
                signal: "CC",
                interrupt: "TIM5",
            },
            PeripheralInterrupt {
                signal: "COM",
                interrupt: "TIM5",
            },
            PeripheralInterrupt {
                signal: "TRG",
                interrupt: "TIM5",
            },
            PeripheralInterrupt {
                signal: "UP",
                interrupt: "TIM5",
            },
        ],
    },
    Peripheral {
        name: "TIM6",
        address: 1073745920,
        registers: Some(
            PeripheralRegisters {
                kind: "timer",
                version: "v1",
                block: "TIM_BASIC",
                ir: &timer::REGISTERS,
            },
        ),
        rcc: Some(
            PeripheralRcc {
                clock: "pclk1_tim",
                enable: Some(
                    PeripheralRccRegister {
                        register: "apb1enr",
                        field: "tim6en",
                    },
                ),
                reset: Some(
                    PeripheralRccRegister {
                        register: "apb1rstr",
                        field: "tim6rst",
                    },
                ),
                mux: None,
                stop_mode: StopMode::Stop1,
            },
        ),
        pins: &[],
        dma_channels: &[
            PeripheralDmaChannel {
                signal: "UP",
                channel: Some(
                    "DMA1_CH1",
                ),
                dmamux: None,
                dma: None,
                request: Some(
                    7,
                ),
            },
        ],
        interrupts: &[
            PeripheralInterrupt {
                signal: "BRK",
                interrupt: "TIM6_DAC",
            },
            PeripheralInterrupt {
                signal: "CC",
                interrupt: "TIM6_DAC",
            },
            PeripheralInterrupt {
                signal: "COM",
                interrupt: "TIM6_DAC",
            },
            PeripheralInterrupt {
                signal: "TRG",
                interrupt: "TIM6_DAC",
            },
            PeripheralInterrupt {
                signal: "UP",
                interrupt: "TIM6_DAC",
            },
        ],
    },
    Peripheral {
        name: "TIM7",
        address: 1073746944,
        registers: Some(
            PeripheralRegisters {
                kind: "timer",
                version: "v1",
                block: "TIM_BASIC",
                ir: &timer::REGISTERS,
            },
        ),
        rcc: Some(
            PeripheralRcc {
                clock: "pclk1_tim",
                enable: Some(
                    PeripheralRccRegister {
                        register: "apb1enr",
                        field: "tim7en",
                    },
                ),
                reset: Some(
                    PeripheralRccRegister {
                        register: "apb1rstr",
                        field: "tim7rst",
                    },
                ),
                mux: None,
                stop_mode: StopMode::Stop1,
            },
        ),
        pins: &[],
        dma_channels: &[
            PeripheralDmaChannel {
                signal: "UP",
                channel: Some(
                    "DMA1_CH2",
                ),
                dmamux: None,
                dma: None,
                request: Some(
                    1,
                ),
            },
            PeripheralDmaChannel {
                signal: "UP",
                channel: Some(
                    "DMA1_CH4",
                ),
                dmamux: None,
                dma: None,
                request: Some(
                    1,
                ),
            },
        ],
        interrupts: &[
            PeripheralInterrupt {
                signal: "BRK",
                interrupt: "TIM7",
            },
            PeripheralInterrupt {
                signal: "CC",
                interrupt: "TIM7",
            },
            PeripheralInterrupt {
                signal: "COM",
                interrupt: "TIM7",
            },
            PeripheralInterrupt {
                signal: "TRG",
                interrupt: "TIM7",
            },
            PeripheralInterrupt {
                signal: "UP",
                interrupt: "TIM7",
            },
        ],
    },
    Peripheral {
        name: "TIM8",
        address: 1073808384,
        registers: Some(
            PeripheralRegisters {
                kind: "timer",
                version: "v1",
                block: "TIM_ADV",
                ir: &timer::REGISTERS,
            },
        ),
        rcc: Some(
            PeripheralRcc {
                clock: "pclk2_tim",
                enable: Some(
                    PeripheralRccRegister {
                        register: "apb2enr",
                        field: "tim8en",
                    },
                ),
                reset: Some(
                    PeripheralRccRegister {
                        register: "apb2rstr",
                        field: "tim8rst",
                    },
                ),
                mux: None,
                stop_mode: StopMode::Stop1,
            },
        ),
        pins: &[
            PeripheralPin {
                pin: "PA0",
                signal: "ETR",
                af: Some(
                    3,
                ),
            },
            PeripheralPin {
                pin: "PA5",
                signal: "CH1N",
                af: Some(
                    3,
                ),
            },
            PeripheralPin {
                pin: "PA6",
                signal: "BKIN",
                af: Some(
                    3,
                ),
            },
            PeripheralPin {
                pin: "PA7",
                signal: "CH1N",
                af: Some(
                    3,
                ),
            },
            PeripheralPin {
                pin: "PB0",
                signal: "CH2N",
                af: Some(
                    3,
                ),
            },
            PeripheralPin {
                pin: "PB1",
                signal: "CH3N",
                af: Some(
                    3,
                ),
            },
            PeripheralPin {
                pin: "PB14",
                signal: "CH2N",
                af: Some(
                    3,
                ),
            },
            PeripheralPin {
                pin: "PB15",
                signal: "CH3N",
                af: Some(
                    3,
                ),
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
            PeripheralInterrupt {
                signal: "UP",
                interrupt: "TIM8_UP_TIM13",
            },
        ],
    },
    Peripheral {
        name: "TIM9",
        address: 1073823744,
        registers: Some(
            PeripheralRegisters {
                kind: "timer",
                version: "v1",
                block: "TIM_GP16",
                ir: &timer::REGISTERS,
            },
        ),
        rcc: Some(
            PeripheralRcc {
                clock: "pclk2_tim",
                enable: Some(
                    PeripheralRccRegister {
                        register: "apb2enr",
                        field: "tim9en",
                    },
                ),
                reset: Some(
                    PeripheralRccRegister {
                        register: "apb2rstr",
                        field: "tim9rst",
                    },
                ),
                mux: None,
                stop_mode: StopMode::Stop1,
            },
        ),
        pins: &[
            PeripheralPin {
                pin: "PA2",
                signal: "CH1",
                af: Some(
                    3,
                ),
            },
            PeripheralPin {
                pin: "PA3",
                signal: "CH2",
                af: Some(
                    3,
                ),
            },
        ],
        dma_channels: &[],
        interrupts: &[
            PeripheralInterrupt {
                signal: "BRK",
                interrupt: "TIM1_BRK_TIM9",
            },
            PeripheralInterrupt {
                signal: "CC",
                interrupt: "TIM1_BRK_TIM9",
            },
            PeripheralInterrupt {
                signal: "COM",
                interrupt: "TIM1_BRK_TIM9",
            },
            PeripheralInterrupt {
                signal: "TRG",
                interrupt: "TIM1_BRK_TIM9",
            },
            PeripheralInterrupt {
                signal: "UP",
                interrupt: "TIM1_BRK_TIM9",
            },
        ],
    },
    Peripheral {
        name: "UART4",
        address: 1073761280,
        registers: None,
        rcc: Some(
            PeripheralRcc {
                clock: "pclk1",
                enable: Some(
                    PeripheralRccRegister {
                        register: "apb1enr",
                        field: "uart4en",
                    },
                ),
                reset: Some(
                    PeripheralRccRegister {
                        register: "apb1rstr",
                        field: "uart4rst",
                    },
                ),
                mux: None,
                stop_mode: StopMode::Stop1,
            },
        ),
        pins: &[
            PeripheralPin {
                pin: "PA0",
                signal: "TX",
                af: Some(
                    8,
                ),
            },
            PeripheralPin {
                pin: "PA1",
                signal: "RX",
                af: Some(
                    8,
                ),
            },
            PeripheralPin {
                pin: "PC10",
                signal: "TX",
                af: Some(
                    8,
                ),
            },
            PeripheralPin {
                pin: "PC11",
                signal: "RX",
                af: Some(
                    8,
                ),
            },
        ],
        dma_channels: &[
            PeripheralDmaChannel {
                signal: "RX",
                channel: Some(
                    "DMA1_CH2",
                ),
                dmamux: None,
                dma: None,
                request: Some(
                    4,
                ),
            },
            PeripheralDmaChannel {
                signal: "TX",
                channel: Some(
                    "DMA1_CH4",
                ),
                dmamux: None,
                dma: None,
                request: Some(
                    4,
                ),
            },
        ],
        interrupts: &[
            PeripheralInterrupt {
                signal: "GLOBAL",
                interrupt: "UART4",
            },
        ],
    },
    Peripheral {
        name: "UART5",
        address: 1073762304,
        registers: None,
        rcc: Some(
            PeripheralRcc {
                clock: "pclk1",
                enable: Some(
                    PeripheralRccRegister {
                        register: "apb1enr",
                        field: "uart5en",
                    },
                ),
                reset: Some(
                    PeripheralRccRegister {
                        register: "apb1rstr",
                        field: "uart5rst",
                    },
                ),
                mux: None,
                stop_mode: StopMode::Stop1,
            },
        ),
        pins: &[
            PeripheralPin {
                pin: "PC12",
                signal: "TX",
                af: Some(
                    8,
                ),
            },
            PeripheralPin {
                pin: "PD2",
                signal: "RX",
                af: Some(
                    8,
                ),
            },
        ],
        dma_channels: &[
            PeripheralDmaChannel {
                signal: "RX",
                channel: Some(
                    "DMA1_CH0",
                ),
                dmamux: None,
                dma: None,
                request: Some(
                    4,
                ),
            },
            PeripheralDmaChannel {
                signal: "TX",
                channel: Some(
                    "DMA1_CH7",
                ),
                dmamux: None,
                dma: None,
                request: Some(
                    4,
                ),
            },
        ],
        interrupts: &[
            PeripheralInterrupt {
                signal: "GLOBAL",
                interrupt: "UART5",
            },
        ],
    },
    Peripheral {
        name: "UID",
        address: 536836624,
        registers: Some(
            PeripheralRegisters {
                kind: "uid",
                version: "v1",
                block: "UID",
                ir: &uid::REGISTERS,
            },
        ),
        rcc: None,
        pins: &[],
        dma_channels: &[],
        interrupts: &[],
    },
    Peripheral {
        name: "USART1",
        address: 1073811456,
        registers: Some(
            PeripheralRegisters {
                kind: "usart",
                version: "v2",
                block: "USART",
                ir: &usart::REGISTERS,
            },
        ),
        rcc: Some(
            PeripheralRcc {
                clock: "pclk2",
                enable: Some(
                    PeripheralRccRegister {
                        register: "apb2enr",
                        field: "usart1en",
                    },
                ),
                reset: Some(
                    PeripheralRccRegister {
                        register: "apb2rstr",
                        field: "usart1rst",
                    },
                ),
                mux: None,
                stop_mode: StopMode::Stop1,
            },
        ),
        pins: &[
            PeripheralPin {
                pin: "PA10",
                signal: "RX",
                af: Some(
                    7,
                ),
            },
            PeripheralPin {
                pin: "PA11",
                signal: "CTS",
                af: Some(
                    7,
                ),
            },
            PeripheralPin {
                pin: "PA12",
                signal: "RTS",
                af: Some(
                    7,
                ),
            },
            PeripheralPin {
                pin: "PA8",
                signal: "CK",
                af: Some(
                    7,
                ),
            },
            PeripheralPin {
                pin: "PA9",
                signal: "TX",
                af: Some(
                    7,
                ),
            },
            PeripheralPin {
                pin: "PB6",
                signal: "TX",
                af: Some(
                    7,
                ),
            },
            PeripheralPin {
                pin: "PB7",
                signal: "RX",
                af: Some(
                    7,
                ),
            },
        ],
        dma_channels: &[
            PeripheralDmaChannel {
                signal: "RX",
                channel: Some(
                    "DMA2_CH2",
                ),
                dmamux: None,
                dma: None,
                request: Some(
                    4,
                ),
            },
            PeripheralDmaChannel {
                signal: "RX",
                channel: Some(
                    "DMA2_CH5",
                ),
                dmamux: None,
                dma: None,
                request: Some(
                    4,
                ),
            },
            PeripheralDmaChannel {
                signal: "TX",
                channel: Some(
                    "DMA2_CH7",
                ),
                dmamux: None,
                dma: None,
                request: Some(
                    4,
                ),
            },
        ],
        interrupts: &[
            PeripheralInterrupt {
                signal: "GLOBAL",
                interrupt: "USART1",
            },
        ],
    },
    Peripheral {
        name: "USART2",
        address: 1073759232,
        registers: Some(
            PeripheralRegisters {
                kind: "usart",
                version: "v2",
                block: "USART",
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
