shufps/eload2/firmware/stm32-metapac/src/chips/metadata_0127.rs

                pub(crate) static PERIPHERALS: &'static [Peripheral] = &[
    Peripheral {
        name: "ADC1",
        address: 1342177280,
        registers: Some(
            PeripheralRegisters {
                kind: "adc",
                version: "f3",
                block: "ADC",
                ir: &adc::REGISTERS,
            },
        ),
        rcc: Some(
            PeripheralRcc {
                clock: "hclk1",
                enable: Some(
                    PeripheralRccRegister {
                        register: "ahbenr",
                        field: "adc12en",
                    },
                ),
                reset: Some(
                    PeripheralRccRegister {
                        register: "ahbrstr",
                        field: "adc12rst",
                    },
                ),
                mux: None,
                stop_mode: StopMode::Stop1,
            },
        ),
        pins: &[
            PeripheralPin {
                pin: "PA0",
                signal: "IN1",
                af: None,
            },
            PeripheralPin {
                pin: "PA1",
                signal: "IN2",
                af: None,
            },
            PeripheralPin {
                pin: "PA2",
                signal: "IN3",
                af: None,
            },
            PeripheralPin {
                pin: "PA3",
                signal: "IN4",
                af: None,
            },
            PeripheralPin {
                pin: "PB11",
                signal: "IN14",
                af: None,
            },
            PeripheralPin {
                pin: "PC0",
                signal: "IN6",
                af: None,
            },
            PeripheralPin {
                pin: "PC1",
                signal: "IN7",
                af: None,
            },
            PeripheralPin {
                pin: "PC2",
                signal: "IN8",
                af: None,
            },
            PeripheralPin {
                pin: "PC3",
                signal: "IN9",
                af: None,
            },
            PeripheralPin {
                pin: "PF2",
                signal: "IN10",
                af: None,
            },
            PeripheralPin {
                pin: "PF4",
                signal: "IN5",
                af: None,
            },
        ],
        dma_channels: &[
            PeripheralDmaChannel {
                signal: "ADC1",
                channel: Some(
                    "DMA1_CH1",
                ),
                dmamux: None,
                dma: None,
                request: None,
            },
        ],
        interrupts: &[
            PeripheralInterrupt {
                signal: "GLOBAL",
                interrupt: "ADC1_2",
            },
        ],
    },
    Peripheral {
        name: "ADC2",
        address: 1342177536,
        registers: Some(
            PeripheralRegisters {
                kind: "adc",
                version: "f3",
                block: "ADC",
                ir: &adc::REGISTERS,
            },
        ),
        rcc: Some(
            PeripheralRcc {
                clock: "hclk1",
                enable: Some(
                    PeripheralRccRegister {
                        register: "ahbenr",
                        field: "adc12en",
                    },
                ),
                reset: Some(
                    PeripheralRccRegister {
                        register: "ahbrstr",
                        field: "adc12rst",
                    },
                ),
                mux: None,
                stop_mode: StopMode::Stop1,
            },
        ),
        pins: &[
            PeripheralPin {
                pin: "PA4",
                signal: "IN1",
                af: None,
            },
            PeripheralPin {
                pin: "PA5",
                signal: "IN2",
                af: None,
            },
            PeripheralPin {
                pin: "PA6",
                signal: "IN3",
                af: None,
            },
            PeripheralPin {
                pin: "PA7",
                signal: "IN4",
                af: None,
            },
            PeripheralPin {
                pin: "PB11",
                signal: "IN14",
                af: None,
            },
            PeripheralPin {
                pin: "PB2",
                signal: "IN12",
                af: None,
            },
            PeripheralPin {
                pin: "PC0",
                signal: "IN6",
                af: None,
            },
            PeripheralPin {
                pin: "PC1",
                signal: "IN7",
                af: None,
            },
            PeripheralPin {
                pin: "PC2",
                signal: "IN8",
                af: None,
            },
            PeripheralPin {
                pin: "PC3",
                signal: "IN9",
                af: None,
            },
            PeripheralPin {
                pin: "PC4",
                signal: "IN5",
                af: None,
            },
            PeripheralPin {
                pin: "PC5",
                signal: "IN11",
                af: None,
            },
            PeripheralPin {
                pin: "PF2",
                signal: "IN10",
                af: None,
            },
        ],
        dma_channels: &[
            PeripheralDmaChannel {
                signal: "ADC2",
                channel: Some(
                    "DMA2_CH1",
                ),
                dmamux: None,
                dma: None,
                request: None,
            },
            PeripheralDmaChannel {
                signal: "ADC2",
                channel: Some(
                    "DMA2_CH3",
                ),
                dmamux: None,
                dma: None,
                request: None,
            },
        ],
        interrupts: &[
            PeripheralInterrupt {
                signal: "GLOBAL",
                interrupt: "ADC1_2",
            },
        ],
    },
    Peripheral {
        name: "ADC_COMMON",
        address: 1342178048,
        registers: Some(
            PeripheralRegisters {
                kind: "adccommon",
                version: "f3",
                block: "ADC_COMMON",
                ir: &adccommon::REGISTERS,
            },
        ),
        rcc: None,
        pins: &[],
        dma_channels: &[],
        interrupts: &[],
    },
    Peripheral {
        name: "CAN",
        address: 1073767424,
        registers: Some(
            PeripheralRegisters {
                kind: "can",
                version: "bxcan",
                block: "CAN",
                ir: &can::REGISTERS,
            },
        ),
        rcc: Some(
            PeripheralRcc {
                clock: "pclk1",
                enable: Some(
                    PeripheralRccRegister {
                        register: "apb1enr",
                        field: "canen",
                    },
                ),
                reset: Some(
                    PeripheralRccRegister {
                        register: "apb1rstr",
                        field: "canrst",
                    },
                ),
                mux: None,
                stop_mode: StopMode::Stop1,
            },
        ),
        pins: &[
            PeripheralPin {
                pin: "PA11",
                signal: "RX",
                af: Some(
                    9,
                ),
            },
            PeripheralPin {
                pin: "PA12",
                signal: "TX",
                af: Some(
                    9,
                ),
            },
            PeripheralPin {
                pin: "PB8",
                signal: "RX",
                af: Some(
                    9,
                ),
            },
            PeripheralPin {
                pin: "PB9",
                signal: "TX",
                af: Some(
                    9,
                ),
            },
            PeripheralPin {
                pin: "PD0",
                signal: "RX",
                af: Some(
                    7,
                ),
            },
            PeripheralPin {
                pin: "PD1",
                signal: "TX",
                af: Some(
                    7,
                ),
            },
        ],
        dma_channels: &[],
        interrupts: &[
            PeripheralInterrupt {
                signal: "RX0",
                interrupt: "USB_LP_CAN_RX0",
            },
            PeripheralInterrupt {
                signal: "RX1",
                interrupt: "CAN_RX1",
            },
            PeripheralInterrupt {
                signal: "SCE",
                interrupt: "CAN_SCE",
            },
            PeripheralInterrupt {
                signal: "TX",
                interrupt: "USB_HP_CAN_TX",
            },
        ],
    },
    Peripheral {
        name: "COMP1",
        address: 1073807388,
        registers: None,
        rcc: None,
        pins: &[
            PeripheralPin {
                pin: "PA0",
                signal: "INM",
                af: None,
            },
            PeripheralPin {
                pin: "PA0",
                signal: "OUT",
                af: Some(
                    8,
                ),
            },
            PeripheralPin {
                pin: "PA1",
                signal: "INP",
                af: None,
            },
            PeripheralPin {
                pin: "PA11",
                signal: "OUT",
                af: Some(
                    8,
                ),
            },
            PeripheralPin {
                pin: "PA4",
                signal: "INM",
                af: None,
            },
            PeripheralPin {
                pin: "PA5",
                signal: "INM",
                af: None,
            },
            PeripheralPin {
                pin: "PA6",
                signal: "OUT",
                af: Some(
                    8,
                ),
            },
            PeripheralPin {
                pin: "PB8",
                signal: "OUT",
                af: Some(
                    8,
                ),
            },
            PeripheralPin {
                pin: "PF4",
                signal: "OUT",
                af: Some(
                    2,
                ),
            },
        ],
        dma_channels: &[],
        interrupts: &[
            PeripheralInterrupt {
                signal: "WKUP",
                interrupt: "COMP1_2",
            },
        ],
    },
    Peripheral {
        name: "COMP2",
        address: 1073807392,
        registers: None,
        rcc: None,
        pins: &[
            PeripheralPin {
                pin: "PA12",
                signal: "OUT",
                af: Some(
                    8,
                ),
            },
            PeripheralPin {
                pin: "PA2",
                signal: "INM",
                af: None,
            },
            PeripheralPin {
                pin: "PA2",
                signal: "OUT",
                af: Some(
                    8,
                ),
            },
            PeripheralPin {
                pin: "PA4",
                signal: "INM",
                af: None,
            },
            PeripheralPin {
                pin: "PA5",
                signal: "INM",
                af: None,
            },
            PeripheralPin {
                pin: "PA7",
                signal: "INP",
                af: None,
            },
            PeripheralPin {
                pin: "PB9",
                signal: "OUT",
                af: Some(
                    8,
                ),
            },
        ],
        dma_channels: &[],
        interrupts: &[
            PeripheralInterrupt {
                signal: "WKUP",
                interrupt: "COMP1_2",
            },
        ],
    },
    Peripheral {
        name: "COMP4",
        address: 1073807400,
        registers: None,
        rcc: None,
        pins: &[
            PeripheralPin {
                pin: "PA4",
                signal: "INM",
                af: None,
            },
            PeripheralPin {
                pin: "PA5",
                signal: "INM",
                af: None,
            },
            PeripheralPin {
                pin: "PB0",
                signal: "INP",
                af: None,
            },
            PeripheralPin {
                pin: "PB1",
                signal: "OUT",
                af: Some(
                    8,
                ),
            },
            PeripheralPin {
                pin: "PB2",
                signal: "INM",
                af: None,
            },
            PeripheralPin {
                pin: "PE8",
                signal: "INM",
                af: None,
            },
        ],
        dma_channels: &[],
        interrupts: &[
            PeripheralInterrupt {
                signal: "WKUP",
                interrupt: "COMP4_6",
            },
        ],
    },
    Peripheral {
        name: "COMP6",
        address: 1073807408,
        registers: None,
        rcc: None,
        pins: &[
            PeripheralPin {
                pin: "PA10",
                signal: "OUT",
                af: Some(
                    8,
                ),
            },
            PeripheralPin {
                pin: "PA4",
                signal: "INM",
                af: None,
            },
            PeripheralPin {
                pin: "PA5",
                signal: "INM",
                af: None,
            },
            PeripheralPin {
                pin: "PB11",
                signal: "INP",
                af: None,
            },
            PeripheralPin {
                pin: "PB15",
                signal: "INM",
                af: None,
            },
            PeripheralPin {
                pin: "PC6",
                signal: "OUT",
                af: Some(
                    7,
                ),
            },
            PeripheralPin {
                pin: "PD10",
                signal: "INM",
                af: None,
            },
        ],
        dma_channels: &[],
        interrupts: &[
            PeripheralInterrupt {
                signal: "WKUP",
                interrupt: "COMP4_6",
            },
        ],
    },
    Peripheral {
        name: "CRC",
        address: 1073885184,
        registers: Some(
            PeripheralRegisters {
                kind: "crc",
                version: "v3",
                block: "CRC",
                ir: &crc::REGISTERS,
            },
        ),
        rcc: Some(
            PeripheralRcc {
                clock: "hclk1",
                enable: Some(
                    PeripheralRccRegister {
                        register: "ahbenr",
                        field: "crcen",
                    },
                ),
                reset: None,
                mux: None,
                stop_mode: StopMode::Stop1,
            },
        ),
        pins: &[],
        dma_channels: &[],
        interrupts: &[],
    },
    Peripheral {
        name: "DAC1",
        address: 1073771520,
        registers: Some(
            PeripheralRegisters {
                kind: "dac",
                version: "v2",
                block: "DAC",
                ir: &dac::REGISTERS,
            },
        ),
        rcc: Some(
            PeripheralRcc {
                clock: "pclk1",
                enable: Some(
                    PeripheralRccRegister {
                        register: "apb1enr",
                        field: "dacen",
                    },
                ),
                reset: Some(
                    PeripheralRccRegister {
                        register: "apb1rstr",
                        field: "dacrst",
                    },
                ),
                mux: None,
                stop_mode: StopMode::Stop1,
            },
        ),
        pins: &[
            PeripheralPin {
                pin: "PA4",
                signal: "OUT1",
                af: None,
            },
        ],
        dma_channels: &[
            PeripheralDmaChannel {
                signal: "CH1",
                channel: Some(
                    "DMA1_CH3",
                ),
                dmamux: None,
                dma: None,
                request: None,
            },
            PeripheralDmaChannel {
                signal: "CH2",
                channel: Some(
                    "DMA1_CH4",
                ),
                dmamux: None,
                dma: None,
                request: None,
            },
            PeripheralDmaChannel {
                signal: "CH1",
                channel: Some(
                    "DMA2_CH3",
                ),
                dmamux: None,
                dma: None,
                request: None,
            },
            PeripheralDmaChannel {
                signal: "CH2",
                channel: Some(
                    "DMA2_CH4",
                ),
                dmamux: None,
                dma: None,
                request: None,
            },
        ],
        interrupts: &[
            PeripheralInterrupt {
                signal: "GLOBAL",
                interrupt: "TIM6_DAC",
            },
        ],
    },
    Peripheral {
        name: "DBGMCU",
        address: 3758366720,
        registers: Some(
            PeripheralRegisters {
                kind: "dbgmcu",
                version: "f3",
                block: "DBGMCU",
                ir: &dbgmcu::REGISTERS,
            },
        ),
        rcc: Some(
            PeripheralRcc {
                clock: "pclk2",
                enable: Some(
                    PeripheralRccRegister {
                        register: "apb2enr",
                        field: "dbgmcuen",
                    },
                ),
                reset: Some(
                    PeripheralRccRegister {
                        register: "apb2rstr",
                        field: "dbgmcurst",
                    },
                ),
                mux: None,
                stop_mode: StopMode::Stop1,
            },
        ),
        pins: &[],
        dma_channels: &[],
        interrupts: &[],
    },
    Peripheral {
        name: "DMA1",
        address: 1073872896,
        registers: Some(
            PeripheralRegisters {
                kind: "bdma",
                version: "v1",
                block: "DMA",
                ir: &bdma::REGISTERS,
            },
        ),
        rcc: Some(
            PeripheralRcc {
                clock: "hclk1",
                enable: Some(
                    PeripheralRccRegister {
                        register: "ahbenr",
                        field: "dma1en",
                    },
                ),
                reset: None,
                mux: None,
                stop_mode: StopMode::Stop1,
            },
        ),
        pins: &[],
        dma_channels: &[],
        interrupts: &[
            PeripheralInterrupt {
                signal: "CH1",
                interrupt: "DMA1_CHANNEL1",
            },
            PeripheralInterrupt {
                signal: "CH2",
                interrupt: "DMA1_CHANNEL2",
            },
            PeripheralInterrupt {
                signal: "CH3",
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
        name: "FLASH",
        address: 1073881088,
        registers: Some(
            PeripheralRegisters {
                kind: "flash",
                version: "f3",
                block: "FLASH",
                ir: &flash::REGISTERS,
            },
        ),
        rcc: Some(
            PeripheralRcc {
                clock: "hclk1",
                enable: Some(
                    PeripheralRccRegister {
                        register: "ahbenr",
                        field: "flashen",
                    },
                ),
                reset: None,
                mux: None,
                stop_mode: StopMode::Stop1,
            },
        ),
        pins: &[],
        dma_channels: &[],
        interrupts: &[
            PeripheralInterrupt {
                signal: "GLOBAL",
                interrupt: "FLASH",
            },
        ],
    },
    Peripheral {
        name: "FMC",
        address: 1610612736,
        registers: None,
        rcc: Some(
            PeripheralRcc {
                clock: "hclk1",
                enable: Some(
                    PeripheralRccRegister {
                        register: "ahbenr",
                        field: "fmcen",
                    },
                ),
                reset: Some(
                    PeripheralRccRegister {
                        register: "ahbrstr",
                        field: "fmcrst",
                    },
                ),
                mux: None,
                stop_mode: StopMode::Stop1,
            },
        ),
        pins: &[
            PeripheralPin {
                pin: "PB7",
                signal: "NL",
                af: Some(
                    12,
                ),
            },
            PeripheralPin {
                pin: "PD0",
                signal: "D2",
                af: Some(
                    12,
                ),
            },
            PeripheralPin {
                pin: "PD0",
                signal: "DA2",
                af: None,
            },
            PeripheralPin {
                pin: "PD1",
                signal: "D3",
                af: Some(
                    12,
                ),
            },
            PeripheralPin {
                pin: "PD1",
                signal: "DA3",
                af: None,
            },
            PeripheralPin {
                pin: "PD10",
                signal: "D15",
                af: Some(
                    12,
                ),
            },
            PeripheralPin {
                pin: "PD10",
                signal: "DA15",
                af: None,
            },
            PeripheralPin {
                pin: "PD11",
                signal: "A16",
                af: Some(
                    12,
                ),
            },
            PeripheralPin {
                pin: "PD11",
                signal: "CLE",
                af: None,
            },
            PeripheralPin {
                pin: "PD12",
                signal: "A17",
                af: Some(
                    12,
                ),
            },
            PeripheralPin {
                pin: "PD12",
                signal: "ALE",
                af: None,
            },
            PeripheralPin {
                pin: "PD13",
                signal: "A18",
                af: Some(
                    12,
                ),
            },
            PeripheralPin {
                pin: "PD14",
                signal: "D0",
                af: Some(
                    12,
                ),
            },
            PeripheralPin {
                pin: "PD14",
                signal: "DA0",
                af: None,
            },
            PeripheralPin {
                pin: "PD15",
                signal: "D1",
                af: Some(
                    12,
                ),
            },
            PeripheralPin {
                pin: "PD15",
                signal: "DA1",
                af: None,
            },
            PeripheralPin {
                pin: "PD3",
                signal: "CLK",
                af: Some(
                    12,
                ),
            },
            PeripheralPin {
                pin: "PD4",
                signal: "NOE",
                af: Some(
                    12,
                ),
            },
            PeripheralPin {
                pin: "PD5",
                signal: "NWE",
                af: Some(
                    12,
                ),
            },
            PeripheralPin {
                pin: "PD6",
                signal: "NWAIT",
                af: Some(
                    12,
                ),
            },
            PeripheralPin {
                pin: "PD7",
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
        name: "GPIOD",
        address: 1207962624,
        registers: Some(
            PeripheralRegisters {
                kind: "gpio",
                version: "v2",
                block: "GPIO",
                ir: &gpio::REGISTERS,
            },
        ),
        rcc: Some(
            PeripheralRcc {
                clock: "hclk1",
                enable: Some(
                    PeripheralRccRegister {
                        register: "ahbenr",
                        field: "gpioden",
                    },
                ),
                reset: Some(
                    PeripheralRccRegister {
                        register: "ahbrstr",
                        field: "gpiodrst",
                    },
                ),
                mux: None,
                stop_mode: StopMode::Stop1,
            },
        ),
        pins: &[],
        dma_channels: &[],
        interrupts: &[],
    },
    Peripheral {
        name: "GPIOE",
        address: 1207963648,
        registers: Some(
            PeripheralRegisters {
                kind: "gpio",
                version: "v2",
                block: "GPIO",
                ir: &gpio::REGISTERS,
            },
        ),
        rcc: Some(
            PeripheralRcc {
                clock: "hclk1",
                enable: Some(
                    PeripheralRccRegister {
                        register: "ahbenr",
                        field: "gpioeen",
                    },
                ),
                reset: Some(
                    PeripheralRccRegister {
                        register: "ahbrstr",
                        field: "gpioerst",
                    },
                ),
                mux: None,
                stop_mode: StopMode::Stop1,
            },
        ),
        pins: &[],
        dma_channels: &[],
        interrupts: &[],
    },
    Peripheral {
        name: "GPIOF",
        address: 1207964672,
        registers: Some(
            PeripheralRegisters {
                kind: "gpio",
                version: "v2",
                block: "GPIO",
                ir: &gpio::REGISTERS,
            },
        ),
        rcc: Some(
            PeripheralRcc {
                clock: "hclk1",
                enable: Some(
                    PeripheralRccRegister {
                        register: "ahbenr",
                        field: "gpiofen",
                    },
                ),
                reset: Some(
                    PeripheralRccRegister {
                        register: "ahbrstr",
                        field: "gpiofrst",
                    },
                ),
                mux: None,
                stop_mode: StopMode::Stop1,
            },
        ),
        pins: &[],
        dma_channels: &[],
        interrupts: &[],
    },
    Peripheral {
        name: "GPIOG",
        address: 1207965696,
        registers: Some(
            PeripheralRegisters {
                kind: "gpio",
                version: "v2",
                block: "GPIO",
                ir: &gpio::REGISTERS,
            },
        ),
        rcc: Some(
            PeripheralRcc {
                clock: "hclk1",
                enable: Some(
                    PeripheralRccRegister {
                        register: "ahbenr",
                        field: "gpiogen",
                    },
                ),
                reset: Some(
                    PeripheralRccRegister {
                        register: "ahbrstr",
                        field: "gpiogrst",
                    },
                ),
                mux: None,
                stop_mode: StopMode::Stop1,
            },
        ),
        pins: &[],
        dma_channels: &[],
        interrupts: &[],
    },
    Peripheral {
        name: "GPIOH",
        address: 1207966720,
        registers: Some(
            PeripheralRegisters {
                kind: "gpio",
                version: "v2",
                block: "GPIO",
                ir: &gpio::REGISTERS,
            },
        ),
        rcc: Some(
            PeripheralRcc {
                clock: "hclk1",
                enable: Some(
                    PeripheralRccRegister {
                        register: "ahbenr",
                        field: "gpiohen",
                    },
                ),
                reset: Some(
                    PeripheralRccRegister {
                        register: "ahbrstr",
                        field: "gpiohrst",
                    },
                ),
                mux: None,
                stop_mode: StopMode::Stop1,
            },
        ),
        pins: &[],
        dma_channels: &[],
        interrupts: &[],
    },
    Peripheral {
        name: "I2C1",
        address: 1073763328,
        registers: Some(
            PeripheralRegisters {
                kind: "i2c",
                version: "v2",
                block: "I2C",
                ir: &i2c::REGISTERS,
            },
        ),
        rcc: Some(
            PeripheralRcc {
                clock: "pclk1",
                enable: Some(
                    PeripheralRccRegister {
                        register: "apb1enr",
                        field: "i2c1en",
                    },
                ),
                reset: Some(
                    PeripheralRccRegister {
                        register: "apb1rstr",
                        field: "i2c1rst",
                    },
                ),
                mux: Some(
                    PeripheralRccRegister {
                        register: "cfgr3",
                        field: "i2c1sw",
                    },
                ),
                stop_mode: StopMode::Stop1,
            },
        ),
        pins: &[
            PeripheralPin {
                pin: "PA14",
                signal: "SDA",
                af: Some(
                    4,
                ),
            },
            PeripheralPin {
                pin: "PA15",
                signal: "SCL",
                af: Some(
                    4,
                ),
            },
            PeripheralPin {
                pin: "PB5",
                signal: "SMBA",
                af: Some(
                    4,
                ),
            },
            PeripheralPin {
                pin: "PB6",
                signal: "SCL",
                af: Some(
                    4,
                ),
            },
            PeripheralPin {
                pin: "PB7",
                signal: "SDA",
                af: Some(
                    4,
                ),
            },
            PeripheralPin {
                pin: "PB8",
                signal: "SCL",
                af: Some(
                    4,
                ),
            },
            PeripheralPin {
                pin: "PB9",
                signal: "SDA",
                af: Some(
                    4,
                ),
            },
        ],
        dma_channels: &[
            PeripheralDmaChannel {
                signal: "TX",
                channel: Some(
                    "DMA1_CH6",
                ),
                dmamux: None,
                dma: None,
                request: None,
            },
            PeripheralDmaChannel {
                signal: "RX",
                channel: Some(
                    "DMA1_CH7",
                ),
                dmamux: None,
                dma: None,
                request: None,
            },
        ],
        interrupts: &[
            PeripheralInterrupt {
                signal: "ER",
                interrupt: "I2C1_ER",
            },
            PeripheralInterrupt {
                signal: "EV",
                interrupt: "I2C1_EV",
            },
        ],
    },
    Peripheral {
        name: "I2C2",
        address: 1073764352,
        registers: Some(
            PeripheralRegisters {
                kind: "i2c",
                version: "v2",
                block: "I2C",
                ir: &i2c::REGISTERS,
            },
        ),
        rcc: Some(
            PeripheralRcc {
                clock: "pclk1",
                enable: Some(
                    PeripheralRccRegister {
                        register: "apb1enr",
                        field: "i2c2en",
                    },
                ),
                reset: Some(
                    PeripheralRccRegister {
                        register: "apb1rstr",
                        field: "i2c2rst",
                    },
                ),
                mux: Some(
                    PeripheralRccRegister {
                        register: "cfgr3",
                        field: "i2c2sw",
                    },
                ),
                stop_mode: StopMode::Stop1,
            },
        ),
        pins: &[
            PeripheralPin {
                pin: "PA10",
                signal: "SDA",
                af: Some(
                    4,
                ),
            },
            PeripheralPin {
                pin: "PA8",
                signal: "SMBA",
                af: Some(
                    4,
                ),
            },
            PeripheralPin {
                pin: "PA9",
                signal: "SCL",
                af: Some(
                    4,
                ),
            },
            PeripheralPin {
                pin: "PB12",
                signal: "SMBA",
                af: Some(
                    4,
                ),
            },
            PeripheralPin {
                pin: "PF0",
                signal: "SDA",
                af: Some(
                    4,
                ),
            },
            PeripheralPin {
                pin: "PF1",
                signal: "SCL",
                af: Some(
                    4,
                ),
            },
            PeripheralPin {
                pin: "PF6",
                signal: "SCL",
                af: Some(
                    4,
                ),
            },
        ],
        dma_channels: &[
            PeripheralDmaChannel {
                signal: "TX",
                channel: Some(
                    "DMA1_CH4",
                ),
                dmamux: None,
                dma: None,
                request: None,
            },
            PeripheralDmaChannel {
                signal: "RX",
                channel: Some(
                    "DMA1_CH5",
                ),
                dmamux: None,
                dma: None,
                request: None,
            },
        ],
        interrupts: &[
            PeripheralInterrupt {
                signal: "ER",
                interrupt: "I2C2_ER",
            },
            PeripheralInterrupt {
                signal: "EV",
                interrupt: "I2C2_EV",
            },
        ],
    },
    Peripheral {
        name: "I2C3",
        address: 1073772544,
        registers: Some(
            PeripheralRegisters {
                kind: "i2c",
                version: "v2",
                block: "I2C",
                ir: &i2c::REGISTERS,
            },
        ),
        rcc: Some(
            PeripheralRcc {
                clock: "pclk1",
                enable: Some(
                    PeripheralRccRegister {
                        register: "apb1enr",
                        field: "i2c3en",
                    },
                ),
                reset: Some(
                    PeripheralRccRegister {
                        register: "apb1rstr",
                        field: "i2c3rst",
                    },
                ),
                mux: Some(
                    PeripheralRccRegister {
                        register: "cfgr3",
                        field: "i2c3sw",
                    },
                ),
                stop_mode: StopMode::Stop1,
            },
        ),
        pins: &[
            PeripheralPin {
                pin: "PA8",
                signal: "SCL",
                af: Some(
                    3,
                ),
            },
            PeripheralPin {
                pin: "PA9",
                signal: "SMBA",
                af: Some(
                    2,
                ),
            },
            PeripheralPin {
                pin: "PB5",
                signal: "SDA",
                af: Some(
                    8,
                ),
            },
            PeripheralPin {
                pin: "PC9",
                signal: "SDA",
                af: Some(
                    3,
                ),
            },
        ],
        dma_channels: &[
            PeripheralDmaChannel {
                signal: "TX",
                channel: Some(
                    "DMA1_CH1",
                ),
                dmamux: None,
                dma: None,
                request: None,
            },
            PeripheralDmaChannel {
                signal: "RX",
                channel: Some(
                    "DMA1_CH2",
                ),
                dmamux: None,
                dma: None,
                request: None,
            },
        ],
        interrupts: &[
            PeripheralInterrupt {
                signal: "ER",
                interrupt: "I2C3_ER",
            },
            PeripheralInterrupt {
                signal: "EV",
                interrupt: "I2C3_EV",
            },
        ],
    },
    Peripheral {
        name: "IWDG",
        address: 1073754112,
        registers: Some(
            PeripheralRegisters {
                kind: "iwdg",
                version: "v2",
                block: "IWDG",
                ir: &iwdg::REGISTERS,
            },
        ),
        rcc: None,
        pins: &[],
        dma_channels: &[],
        interrupts: &[],
    },
    Peripheral {
        name: "OPAMP1",
        address: 1073807416,
        registers: Some(
            PeripheralRegisters {
                kind: "opamp",
                version: "f3",
                block: "OPAMP",
                ir: &opamp::REGISTERS,
            },
        ),
        rcc: None,
        pins: &[
            PeripheralPin {
                pin: "PA1",
                signal: "VINP",
                af: None,
            },
            PeripheralPin {
                pin: "PA1",
                signal: "VINP_SEC",
                af: None,
            },
            PeripheralPin {
                pin: "PA2",
                signal: "VOUT",
                af: None,
            },
            PeripheralPin {
                pin: "PA3",
                signal: "VINM",
                af: None,
            },
            PeripheralPin {
                pin: "PA3",
                signal: "VINM_SEC",
                af: None,
            },
            PeripheralPin {
                pin: "PA3",
                signal: "VINP",
                af: None,
            },
            PeripheralPin {
                pin: "PA3",
                signal: "VINP_SEC",
                af: None,
            },
            PeripheralPin {
                pin: "PA5",
                signal: "VINP",
                af: None,
            },
            PeripheralPin {
                pin: "PA5",
                signal: "VINP_SEC",
                af: None,
            },
            PeripheralPin {
                pin: "PA7",
                signal: "VINP",
                af: None,
            },
            PeripheralPin {
                pin: "PA7",
                signal: "VINP_SEC",
                af: None,
            },
            PeripheralPin {
                pin: "PC5",
                signal: "VINM",
                af: None,
            },
            PeripheralPin {
                pin: "PC5",
                signal: "VINM_SEC",
                af: None,
            },
            PeripheralPin {
                pin: "PA7",
                signal: "VP0",
                af: None,
            },
            PeripheralPin {
                pin: "PA5",
                signal: "VP1",
                af: None,
            },
            PeripheralPin {
                pin: "PA3",
                signal: "VP2",
                af: None,
            },
            PeripheralPin {
                pin: "PA1",
                signal: "VP3",
                af: None,
            },
        ],
        dma_channels: &[],
        interrupts: &[],
    },
    Peripheral {
        name: "OPAMP2",
        address: 1073807420,
        registers: Some(
            PeripheralRegisters {
                kind: "opamp",
                version: "f3",
                block: "OPAMP",
                ir: &opamp::REGISTERS,
            },
        ),
        rcc: None,
        pins: &[
            PeripheralPin {
                pin: "PA5",
                signal: "VINM",
                af: None,
            },
            PeripheralPin {
                pin: "PA5",
                signal: "VINM_SEC",
                af: None,
            },
            PeripheralPin {
                pin: "PA6",
                signal: "VOUT",
                af: None,
            },
            PeripheralPin {
                pin: "PA7",
                signal: "VINP",
                af: None,
            },
            PeripheralPin {
                pin: "PA7",
                signal: "VINP_SEC",
                af: None,
            },
            PeripheralPin {
                pin: "PB0",
                signal: "VINP",
                af: None,
            },
            PeripheralPin {
                pin: "PB0",
                signal: "VINP_SEC",
                af: None,
            },
            PeripheralPin {
                pin: "PB14",
                signal: "VINP",
                af: None,
            },
            PeripheralPin {
                pin: "PB14",
                signal: "VINP_SEC",
                af: None,
            },
            PeripheralPin {
                pin: "PC5",
                signal: "VINM",
                af: None,
            },
            PeripheralPin {
                pin: "PC5",
                signal: "VINM_SEC",
                af: None,
            },
            PeripheralPin {
                pin: "PD14",
                signal: "VINP",
                af: None,
            },
            PeripheralPin {
                pin: "PD14",
                signal: "VINP_SEC",
                af: None,
            },
            PeripheralPin {
                pin: "PD14",
                signal: "VP0",
                af: None,
            },
            PeripheralPin {
                pin: "PB14",
                signal: "VP1",
                af: None,
            },
            PeripheralPin {
                pin: "PB0",
                signal: "VP2",
                af: None,
            },
            PeripheralPin {
                pin: "PA7",
                signal: "VP3",
                af: None,
            },
        ],
        dma_channels: &[],
        interrupts: &[],
    },
    Peripheral {
        name: "PWR",
        address: 1073770496,
        registers: Some(
            PeripheralRegisters {
                kind: "pwr",
                version: "f3",
                block: "PWR",
                ir: &pwr::REGISTERS,
            },
        ),
        rcc: Some(
            PeripheralRcc {
                clock: "pclk1",
                enable: Some(
                    PeripheralRccRegister {
                        register: "apb1enr",
                        field: "pwren",
                    },
                ),
                reset: Some(
                    PeripheralRccRegister {
                        register: "apb1rstr",
                        field: "pwrrst",
                    },
                ),
                mux: None,
                stop_mode: StopMode::Stop1,
            },
        ),
        pins: &[],
        dma_channels: &[],
        interrupts: &[],
    },
    Peripheral {
        name: "RCC",
        address: 1073876992,
        registers: Some(
            PeripheralRegisters {
                kind: "rcc",
                version: "f3",
                block: "RCC",
                ir: &rcc::REGISTERS,
            },
        ),
        rcc: None,
        pins: &[
            PeripheralPin {
                pin: "PA8",
                signal: "MCO",
                af: Some(
                    0,
                ),
            },
            PeripheralPin {
                pin: "PC14",
                signal: "OSC32_IN",
                af: None,
            },
            PeripheralPin {
                pin: "PC15",
                signal: "OSC32_OUT",
                af: None,
            },
            PeripheralPin {
                pin: "PF0",
                signal: "OSC_IN",
                af: None,
            },
            PeripheralPin {
                pin: "PF1",
                signal: "OSC_OUT",
                af: None,
            },
        ],
        dma_channels: &[],
        interrupts: &[
            PeripheralInterrupt {
                signal: "GLOBAL",
                interrupt: "RCC",
            },
        ],
    },
    Peripheral {
        name: "RTC",
        address: 1073752064,
        registers: Some(
            PeripheralRegisters {
                kind: "rtc",
                version: "v2f3",
                block: "RTC",
                ir: &rtc::REGISTERS,
            },
        ),
        rcc: None,
        pins: &[
            PeripheralPin {
                pin: "PA0",
                signal: "TAMP2",
                af: None,
            },
            PeripheralPin {
                pin: "PA1",
                signal: "REFIN",
                af: Some(
                    0,
                ),
            },
            PeripheralPin {
                pin: "PB15",
                signal: "REFIN",
                af: Some(
                    0,
                ),
            },
            PeripheralPin {
                pin: "PC13",
                signal: "OUT_ALARM",
                af: None,
            },
            PeripheralPin {
                pin: "PC13",
                signal: "OUT_CALIB",
                af: None,
            },
            PeripheralPin {
                pin: "PC13",
                signal: "TAMP1",
                af: None,
            },
            PeripheralPin {
                pin: "PC13",
                signal: "TS",
                af: None,
            },
            PeripheralPin {
                pin: "PE6",
                signal: "TAMP3",
                af: None,
            },
        ],
        dma_channels: &[],
        interrupts: &[
            PeripheralInterrupt {
                signal: "ALARM",
                interrupt: "RTC_ALARM",
            },
            PeripheralInterrupt {
                signal: "STAMP",
                interrupt: "TAMP_STAMP",
            },
            PeripheralInterrupt {
                signal: "TAMP",
                interrupt: "TAMP_STAMP",
            },
            PeripheralInterrupt {
                signal: "WKUP",
                interrupt: "RTC_WKUP",
            },
        ],
    },
    Peripheral {
        name: "SPI1",
        address: 1073819648,
        registers: Some(
            PeripheralRegisters {
                kind: "spi",
                version: "v2",
                block: "SPI",
                ir: &spi::REGISTERS,
            },
        ),
        rcc: Some(
            PeripheralRcc {
                clock: "pclk2",
                enable: Some(
                    PeripheralRccRegister {
                        register: "apb2enr",
                        field: "spi1en",
                    },
                ),
                reset: Some(
                    PeripheralRccRegister {
                        register: "apb2rstr",
                        field: "spi1rst",
                    },
                ),
                mux: None,
                stop_mode: StopMode::Stop1,
            },
        ),
        pins: &[
            PeripheralPin {
                pin: "PA15",
                signal: "NSS",
                af: Some(
                    5,
                ),
            },
            PeripheralPin {
                pin: "PA4",
                signal: "NSS",
                af: Some(
                    5,
                ),
            },
            PeripheralPin {
                pin: "PA5",
                signal: "SCK",
                af: Some(
                    5,
                ),
            },
            PeripheralPin {
                pin: "PA6",
                signal: "MISO",
                af: Some(
                    5,
                ),
            },
            PeripheralPin {
                pin: "PA7",
                signal: "MOSI",
                af: Some(
                    5,
                ),
            },
            PeripheralPin {
                pin: "PB3",
                signal: "SCK",
                af: Some(
                    5,
                ),
            },
            PeripheralPin {
                pin: "PB4",
                signal: "MISO",
                af: Some(
                    5,
                ),
            },
            PeripheralPin {
                pin: "PB5",
                signal: "MOSI",
                af: Some(
                    5,
                ),
            },
        ],
        dma_channels: &[
            PeripheralDmaChannel {
                signal: "RX",
                channel: Some(
                    "DMA1_CH2",
                ),
                dmamux: None,
                dma: None,
                request: None,
            },
            PeripheralDmaChannel {
                signal: "TX",
                channel: Some(
                    "DMA1_CH3",
                ),
                dmamux: None,
                dma: None,
                request: None,
            },
        ],
        interrupts: &[
            PeripheralInterrupt {
                signal: "GLOBAL",
                interrupt: "SPI1",
            },
        ],
    },
    Peripheral {
        name: "SPI2",
        address: 1073756160,
        registers: Some(
            PeripheralRegisters {
                kind: "spi",
                version: "v2",
                block: "SPI",
                ir: &spi::REGISTERS,
            },
        ),
        rcc: Some(
            PeripheralRcc {
                clock: "pclk1",
                enable: Some(
                    PeripheralRccRegister {
                        register: "apb1enr",
                        field: "spi2en",
                    },
                ),
                reset: Some(
                    PeripheralRccRegister {
                        register: "apb1rstr",
                        field: "spi2rst",
                    },
                ),
                mux: None,
                stop_mode: StopMode::Stop1,
            },
        ),
        pins: &[
            PeripheralPin {
                pin: "PA10",
                signal: "I2S_ext_SD",
                af: Some(
                    5,
                ),
            },
            PeripheralPin {
                pin: "PA10",
                signal: "MISO",
                af: Some(
                    5,
                ),
            },
            PeripheralPin {
                pin: "PA11",
                signal: "I2S_SD",
                af: Some(
                    5,
                ),
            },
            PeripheralPin {
                pin: "PA11",
                signal: "MOSI",
                af: Some(
                    5,
                ),
            },
            PeripheralPin {
                pin: "PA8",
                signal: "I2S_MCK",
                af: Some(
                    5,
                ),
            },
            PeripheralPin {
                pin: "PB12",
                signal: "I2S_WS",
                af: Some(
                    5,
                ),
            },
            PeripheralPin {
                pin: "PB12",
                signal: "NSS",
                af: Some(
                    5,
                ),
            },
            PeripheralPin {
                pin: "PB13",
                signal: "I2S_CK",
                af: Some(
                    5,
                ),
            },
            PeripheralPin {
                pin: "PB13",
                signal: "SCK",
                af: Some(
                    5,
                ),
            },
            PeripheralPin {
                pin: "PB14",
                signal: "I2S_ext_SD",
                af: Some(
                    5,
                ),
            },
            PeripheralPin {
                pin: "PB14",
                signal: "MISO",
                af: Some(
                    5,
                ),
            },
            PeripheralPin {
                pin: "PB15",
                signal: "I2S_SD",
                af: Some(
                    5,
                ),
            },
            PeripheralPin {
                pin: "PB15",
                signal: "MOSI",
                af: Some(
                    5,
                ),
            },
            PeripheralPin {
                pin: "PC6",
                signal: "I2S_MCK",
                af: Some(
                    6,
                ),
            },
            PeripheralPin {
                pin: "PD15",
                signal: "NSS",
                af: Some(
                    6,
                ),
            },
            PeripheralPin {
                pin: "PF0",
                signal: "I2S_WS",
                af: Some(
                    5,
                ),
            },
            PeripheralPin {
                pin: "PF0",
                signal: "NSS",
                af: Some(
                    5,
                ),
            },
            PeripheralPin {
                pin: "PF1",
                signal: "I2S_CK",
                af: Some(
                    5,
                ),
            },
            PeripheralPin {
                pin: "PF1",
                signal: "SCK",
                af: Some(
                    5,
                ),
            },
            PeripheralPin {
                pin: "PF10",
                signal: "SCK",
                af: Some(
                    5,
                ),
            },
            PeripheralPin {
                pin: "PF9",
                signal: "SCK",
                af: Some(
                    5,
                ),
            },
        ],
        dma_channels: &[
            PeripheralDmaChannel {
                signal: "RX",
                channel: Some(
                    "DMA1_CH4",
                ),
                dmamux: None,
                dma: None,
                request: None,
            },
            PeripheralDmaChannel {
                signal: "TX",
                channel: Some(
                    "DMA1_CH5",
                ),
                dmamux: None,
                dma: None,
                request: None,
            },
        ],
        interrupts: &[
            PeripheralInterrupt {
                signal: "GLOBAL",
                interrupt: "SPI2",
            },
        ],
    },
    Peripheral {
        name: "SPI3",
        address: 1073757184,
        registers: Some(
            PeripheralRegisters {
                kind: "spi",
                version: "v2",
                block: "SPI",
                ir: &spi::REGISTERS,
            },
        ),
        rcc: Some(
            PeripheralRcc {
                clock: "pclk1",
                enable: Some(
                    PeripheralRccRegister {
                        register: "apb1enr",
                        field: "spi3en",
                    },
                ),
                reset: Some(
                    PeripheralRccRegister {
                        register: "apb1rstr",
                        field: "spi3rst",
                    },
                ),
                mux: None,
                stop_mode: StopMode::Stop1,
            },
        ),
        pins: &[
            PeripheralPin {
                pin: "PA15",
                signal: "I2S_WS",
                af: Some(
                    6,
                ),
            },
            PeripheralPin {
                pin: "PA15",
                signal: "NSS",
                af: Some(
                    6,
                ),
            },
            PeripheralPin {
                pin: "PA4",
                signal: "I2S_WS",
                af: Some(
                    6,
                ),
            },
            PeripheralPin {
                pin: "PA4",
                signal: "NSS",
                af: Some(
                    6,
                ),
            },
            PeripheralPin {
                pin: "PA9",
                signal: "I2S_MCK",
                af: Some(
                    5,
                ),
            },
            PeripheralPin {
                pin: "PB3",
                signal: "I2S_CK",
                af: Some(
                    6,
                ),
            },
            PeripheralPin {
                pin: "PB3",
                signal: "SCK",
                af: Some(
                    6,
                ),
            },
            PeripheralPin {
                pin: "PB4",
                signal: "I2S_ext_SD",
                af: Some(
                    6,
                ),
            },
            PeripheralPin {
                pin: "PB4",
                signal: "MISO",
                af: Some(
                    6,
                ),
            },
            PeripheralPin {
                pin: "PB5",
                signal: "I2S_SD",
                af: Some(
                    6,
                ),
            },
            PeripheralPin {
                pin: "PB5",
                signal: "MOSI",
                af: Some(
                    6,
                ),
            },
            PeripheralPin {
                pin: "PC10",
                signal: "I2S_CK",
                af: Some(
                    6,
                ),
            },
            PeripheralPin {
                pin: "PC10",
                signal: "SCK",
                af: Some(
                    6,
                ),
            },
            PeripheralPin {
                pin: "PC11",
                signal: "I2S_ext_SD",
                af: Some(
                    6,
                ),
            },
            PeripheralPin {
                pin: "PC11",
                signal: "MISO",
                af: Some(
                    6,
                ),
            },
            PeripheralPin {
                pin: "PC12",
                signal: "I2S_SD",
                af: Some(
                    6,
                ),
            },
            PeripheralPin {
                pin: "PC12",
                signal: "MOSI",
                af: Some(
                    6,
                ),
            },
            PeripheralPin {
                pin: "PC7",
                signal: "I2S_MCK",
                af: Some(
                    6,
                ),
            },
        ],
        dma_channels: &[
            PeripheralDmaChannel {
                signal: "RX",
                channel: Some(
                    "DMA2_CH1",
                ),
                dmamux: None,
                dma: None,
                request: None,
            },
            PeripheralDmaChannel {
                signal: "TX",
                channel: Some(
                    "DMA2_CH2",
                ),
                dmamux: None,
                dma: None,
                request: None,
            },
        ],
        interrupts: &[
            PeripheralInterrupt {
                signal: "GLOBAL",
                interrupt: "SPI3",
            },
        ],
    },
    Peripheral {
        name: "SPI4",
        address: 1073822720,
        registers: Some(
            PeripheralRegisters {
                kind: "spi",
                version: "v2",
                block: "SPI",
                ir: &spi::REGISTERS,
            },
        ),
        rcc: Some(
            PeripheralRcc {
                clock: "pclk2",
                enable: Some(
                    PeripheralRccRegister {
                        register: "apb2enr",
                        field: "spi4en",
                    },
                ),
                reset: Some(
                    PeripheralRccRegister {
                        register: "apb2rstr",
                        field: "spi4rst",
                    },
                ),
                mux: None,
                stop_mode: StopMode::Stop1,
            },
        ),
        pins: &[
            PeripheralPin {
                pin: "PE11",
                signal: "NSS",
                af: Some(
                    5,
                ),
            },
            PeripheralPin {
                pin: "PE12",
                signal: "SCK",
                af: Some(
                    5,
                ),
            },
            PeripheralPin {
                pin: "PE13",
                signal: "MISO",
                af: Some(
                    5,
                ),
            },
            PeripheralPin {
                pin: "PE14",
                signal: "MOSI",
                af: Some(
                    5,
                ),
            },
            PeripheralPin {
                pin: "PE2",
                signal: "SCK",
                af: Some(
                    5,
                ),
            },
            PeripheralPin {
                pin: "PE3",
                signal: "NSS",
                af: Some(
                    5,
                ),
            },
            PeripheralPin {
                pin: "PE4",
                signal: "NSS",
                af: Some(
                    5,
                ),
            },
            PeripheralPin {
                pin: "PE5",
                signal: "MISO",
                af: Some(
                    5,
                ),
            },
            PeripheralPin {
                pin: "PE6",
                signal: "MOSI",
                af: Some(
                    5,
                ),
            },
        ],
        dma_channels: &[
            PeripheralDmaChannel {
                signal: "RX",
                channel: Some(
                    "DMA2_CH4",
                ),
                dmamux: None,
                dma: None,
                request: None,
            },
            PeripheralDmaChannel {
                signal: "TX",
                channel: Some(
                    "DMA2_CH5",
                ),
                dmamux: None,
                dma: None,
                request: None,
            },
        ],
        interrupts: &[
            PeripheralInterrupt {
                signal: "GLOBAL",
                interrupt: "SPI4",
            },
        ],
    },
    Peripheral {
        name: "SYSCFG",
        address: 1073807360,
        registers: Some(
            PeripheralRegisters {
                kind: "syscfg",
                version: "f3",
                block: "SYSCFG",
                ir: &syscfg::REGISTERS,
            },
        ),
        rcc: Some(
            PeripheralRcc {
                clock: "pclk2",
                enable: Some(
                    PeripheralRccRegister {
                        register: "apb2enr",
                        field: "syscfgen",
                    },
                ),
                reset: Some(
                    PeripheralRccRegister {
                        register: "apb2rstr",
                        field: "syscfgrst",
                    },
                ),
                mux: None,
                stop_mode: StopMode::Stop1,
            },
        ),
        pins: &[],
        dma_channels: &[],
        interrupts: &[],
    },
    Peripheral {
        name: "TIM1",
        address: 1073818624,
        registers: Some(
            PeripheralRegisters {
                kind: "timer",
                version: "v1",
                block: "TIM_ADV",
                ir: &timer::REGISTERS,
            },
        ),
        rcc: Some(
            PeripheralRcc {
                clock: "pclk2_tim",
                enable: Some(
                    PeripheralRccRegister {
                        register: "apb2enr",
                        field: "tim1en",
                    },
                ),
                reset: Some(
                    PeripheralRccRegister {
                        register: "apb2rstr",
                        field: "tim1rst",
                    },
                ),
                mux: Some(
                    PeripheralRccRegister {
                        register: "cfgr3",
                        field: "tim1sw",
                    },
                ),
                stop_mode: StopMode::Stop1,
            },
        ),
        pins: &[
            PeripheralPin {
                pin: "PA10",
                signal: "CH3",
                af: Some(
                    6,
                ),
            },
            PeripheralPin {
                pin: "PA11",
                signal: "BKIN2",
                af: Some(
                    12,
                ),
            },
            PeripheralPin {
                pin: "PA11",
                signal: "CH1N",
                af: Some(
                    6,
                ),
            },
            PeripheralPin {
                pin: "PA11",
                signal: "CH4",
                af: Some(
                    11,
                ),
            },
            PeripheralPin {
                pin: "PA12",
                signal: "CH2N",
                af: Some(
                    6,
                ),
            },
            PeripheralPin {
                pin: "PA12",
                signal: "ETR",
                af: Some(
                    11,
                ),
            },
            PeripheralPin {
                pin: "PA14",
                signal: "BKIN",
                af: Some(
                    6,
                ),
            },
            PeripheralPin {
                pin: "PA15",
                signal: "BKIN",
                af: Some(
                    9,
                ),
            },
            PeripheralPin {
                pin: "PA6",
                signal: "BKIN",
                af: Some(
                    6,
                ),
            },
            PeripheralPin {
                pin: "PA7",
                signal: "CH1N",
                af: Some(
                    6,
                ),
            },
            PeripheralPin {
                pin: "PA8",
                signal: "CH1",
                af: Some(
                    6,
                ),
            },
            PeripheralPin {
                pin: "PA9",
                signal: "CH2",
                af: Some(
                    6,
                ),
            },
            PeripheralPin {
                pin: "PB0",
                signal: "CH2N",
                af: Some(
                    6,
                ),
            },
            PeripheralPin {
                pin: "PB1",
                signal: "CH3N",
                af: Some(
                    6,
                ),
            },
            PeripheralPin {
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
                signal: "CH2",
                channel: Some(
                    "DMA1_CH3",
                ),
                dmamux: None,
                dma: None,
                request: None,
            },
            PeripheralDmaChannel {
                signal: "CH4",
                channel: Some(
                    "DMA1_CH4",
                ),
                dmamux: None,
                dma: None,
                request: None,
            },
            PeripheralDmaChannel {
                signal: "TRIG",
                channel: Some(
                    "DMA1_CH4",
                ),
                dmamux: None,
                dma: None,
                request: None,
            },
            PeripheralDmaChannel {
                signal: "COM",
                channel: Some(
                    "DMA1_CH4",
                ),
                dmamux: None,
                dma: None,
                request: None,
            },
            PeripheralDmaChannel {
                signal: "UP",
                channel: Some(
                    "DMA1_CH5",
                ),
                dmamux: None,
                dma: None,
                request: None,
            },
            PeripheralDmaChannel {
                signal: "CH3",
                channel: Some(
                    "DMA1_CH6",
                ),
                dmamux: None,
                dma: None,
                request: None,
            },
        ],
        interrupts: &[
            PeripheralInterrupt {
                signal: "BRK",
                interrupt: "TIM1_BRK_TIM15",
            },
            PeripheralInterrupt {
                signal: "CC",
                interrupt: "TIM1_CC",
            },
            PeripheralInterrupt {
                signal: "COM",
                interrupt: "TIM1_TRG_COM_TIM17",
            },
            PeripheralInterrupt {
                signal: "TRG",
                interrupt: "TIM1_TRG_COM_TIM17",
            },
            PeripheralInterrupt {
                signal: "UP",
                interrupt: "TIM1_UP_TIM16",
            },
        ],
    },
    Peripheral {
        name: "TIM15",
        address: 1073823744,
        registers: Some(
            PeripheralRegisters {
                kind: "timer",
                version: "v1",
                block: "TIM_GP16",
                ir: &timer::REGISTERS,
            },
        ),
        rcc: Some(
            PeripheralRcc {
                clock: "pclk2_tim",
                enable: Some(
                    PeripheralRccRegister {
                        register: "apb2enr",
                        field: "tim15en",
                    },
                ),
                reset: Some(
                    PeripheralRccRegister {
                        register: "apb2rstr",
                        field: "tim15rst",
                    },
                ),
                mux: Some(
                    PeripheralRccRegister {
                        register: "cfgr3",
                        field: "tim15sw",
                    },
                ),
                stop_mode: StopMode::Stop1,
            },
        ),
        pins: &[
            PeripheralPin {
                pin: "PA1",
                signal: "CH1N",
                af: Some(
                    9,
                ),
            },
            PeripheralPin {
                pin: "PA2",
                signal: "CH1",
                af: Some(
                    9,
                ),
            },
            PeripheralPin {
                pin: "PA3",
                signal: "CH2",
                af: Some(
                    9,
                ),
            },
            PeripheralPin {
                pin: "PA9",
                signal: "BKIN",
                af: Some(
                    9,
                ),
            },
            PeripheralPin {
                pin: "PB14",
                signal: "CH1",
                af: Some(
                    1,
                ),
            },
            PeripheralPin {
                pin: "PB15",
                signal: "CH1N",
                af: Some(
                    2,
                ),
            },
            PeripheralPin {
                pin: "PB15",
                signal: "CH2",
                af: Some(
                    1,
                ),
            },
            PeripheralPin {
                pin: "PC5",
                signal: "BKIN",
                af: Some(
                    2,
                ),
            },
            PeripheralPin {
                pin: "PF10",
                signal: "CH2",
                af: Some(
                    3,
                ),
            },
            PeripheralPin {
                pin: "PF9",
                signal: "CH1",
                af: Some(
                    3,
                ),
            },
        ],
        dma_channels: &[
            PeripheralDmaChannel {
                signal: "CH1",
                channel: Some(
                    "DMA1_CH5",
                ),
                dmamux: None,
                dma: None,
                request: None,
            },
            PeripheralDmaChannel {
                signal: "UP",
                channel: Some(
                    "DMA1_CH5",
                ),
                dmamux: None,
                dma: None,
                request: None,
            },
            PeripheralDmaChannel {
                signal: "TRIG",
                channel: Some(
                    "DMA1_CH5",
                ),
                dmamux: None,
                dma: None,
                request: None,
            },
            PeripheralDmaChannel {
                signal: "COM",
                channel: Some(
                    "DMA1_CH5",
                ),
                dmamux: None,
                dma: None,
                request: None,
            },
        ],
        interrupts: &[
            PeripheralInterrupt {
                signal: "BRK",
                interrupt: "TIM1_BRK_TIM15",
            },
            PeripheralInterrupt {
                signal: "CC",
                interrupt: "TIM1_BRK_TIM15",
            },
            PeripheralInterrupt {
                signal: "COM",
                interrupt: "TIM1_BRK_TIM15",
            },
            PeripheralInterrupt {
                signal: "TRG",
                interrupt: "TIM1_BRK_TIM15",
            },
            PeripheralInterrupt {
                signal: "UP",
                interrupt: "TIM1_BRK_TIM15",
            },
        ],
    },
    Peripheral {
        name: "TIM16",
        address: 1073824768,
        registers: Some(
            PeripheralRegisters {
                kind: "timer",
                version: "v1",
                block: "TIM_GP16",
                ir: &timer::REGISTERS,
            },
        ),
        rcc: Some(
            PeripheralRcc {
                clock: "pclk2_tim",
                enable: Some(
                    PeripheralRccRegister {
                        register: "apb2enr",
                        field: "tim16en",
                    },
                ),
                reset: Some(
                    PeripheralRccRegister {
                        register: "apb2rstr",
                        field: "tim16rst",
                    },
                ),
                mux: Some(
                    PeripheralRccRegister {
                        register: "cfgr3",
                        field: "tim16sw",
                    },
                ),
                stop_mode: StopMode::Stop1,
            },
        ),
        pins: &[
            PeripheralPin {
                pin: "PA12",
                signal: "CH1",
                af: Some(
                    1,
                ),
            },
            PeripheralPin {
                pin: "PA13",
                signal: "CH1N",
                af: Some(
                    1,
                ),
            },
            PeripheralPin {
                pin: "PA6",
                signal: "CH1",
                af: Some(
                    1,
                ),
            },
            PeripheralPin {
                pin: "PB4",
                signal: "CH1",
                af: Some(
                    1,
                ),
            },
            PeripheralPin {
                pin: "PB5",
                signal: "BKIN",
                af: Some(
                    1,
                ),
            },
            PeripheralPin {
                pin: "PB6",
                signal: "CH1N",
                af: Some(
                    1,
                ),
            },
            PeripheralPin {
                pin: "PB8",
                signal: "CH1",
                af: Some(
                    1,
                ),
            },
            PeripheralPin {
                pin: "PE0",
                signal: "CH1",
                af: Some(
                    4,
                ),
            },
        ],
        dma_channels: &[
            PeripheralDmaChannel {
                signal: "CH1",
                channel: Some(
                    "DMA1_CH3",
                ),
                dmamux: None,
                dma: None,
                request: None,
            },
            PeripheralDmaChannel {
                signal: "UP",
                channel: Some(
                    "DMA1_CH3",
                ),
                dmamux: None,
                dma: None,
                request: None,
            },
            PeripheralDmaChannel {
                signal: "CH1",
                channel: Some(
                    "DMA1_CH6",
                ),
                dmamux: None,
                dma: None,
                request: None,
            },
            PeripheralDmaChannel {
                signal: "UP",
                channel: Some(
                    "DMA1_CH6",
                ),
                dmamux: None,
                dma: None,
                request: None,
            },
        ],
        interrupts: &[
            PeripheralInterrupt {
                signal: "BRK",
                interrupt: "TIM1_UP_TIM16",
            },
            PeripheralInterrupt {
                signal: "CC",
                interrupt: "TIM1_UP_TIM16",
            },
            PeripheralInterrupt {
                signal: "COM",
                interrupt: "TIM1_UP_TIM16",
            },
            PeripheralInterrupt {
                signal: "TRG",
                interrupt: "TIM1_UP_TIM16",
            },
            PeripheralInterrupt {
                signal: "UP",
                interrupt: "TIM1_UP_TIM16",
            },
        ],
    },
    Peripheral {
        name: "TIM17",
        address: 1073825792,
        registers: Some(
            PeripheralRegisters {
                kind: "timer",
                version: "v1",
                block: "TIM_GP16",
                ir: &timer::REGISTERS,
            },
        ),
        rcc: Some(
            PeripheralRcc {
                clock: "pclk2_tim",
                enable: Some(
                    PeripheralRccRegister {
                        register: "apb2enr",
                        field: "tim17en",
                    },
                ),
                reset: Some(
                    PeripheralRccRegister {
                        register: "apb2rstr",
                        field: "tim17rst",
                    },
                ),
                mux: Some(
                    PeripheralRccRegister {
                        register: "cfgr3",
                        field: "tim17sw",
                    },
                ),
                stop_mode: StopMode::Stop1,
            },
        ),
        pins: &[
            PeripheralPin {
                pin: "PA10",
                signal: "BKIN",
                af: Some(
                    1,
                ),
            },
            PeripheralPin {
                pin: "PA7",
                signal: "CH1",
                af: Some(
                    1,
                ),
            },
            PeripheralPin {
                pin: "PB4",
                signal: "BKIN",
                af: Some(
                    10,
                ),
            },
            PeripheralPin {
                pin: "PB5",
                signal: "CH1",
                af: Some(
                    10,
                ),
            },
            PeripheralPin {
                pin: "PB7",
                signal: "CH1N",
                af: Some(
                    1,
                ),
            },
            PeripheralPin {
                pin: "PB9",
                signal: "CH1",
                af: Some(
                    1,
                ),
            },
            PeripheralPin {
                pin: "PE1",
                signal: "CH1",
                af: Some(
                    4,
                ),
            },
        ],
        dma_channels: &[
            PeripheralDmaChannel {
                signal: "CH1",
                channel: Some(
                    "DMA1_CH1",
                ),
                dmamux: None,
                dma: None,
                request: None,
            },
            PeripheralDmaChannel {
                signal: "UP",
                channel: Some(
                    "DMA1_CH1",
                ),
                dmamux: None,
                dma: None,
                request: None,
            },
            PeripheralDmaChannel {
                signal: "CH1",
                channel: Some(
                    "DMA1_CH7",
                ),
                dmamux: None,
                dma: None,
                request: None,
            },
            PeripheralDmaChannel {
                signal: "UP",
                channel: Some(
                    "DMA1_CH7",
                ),
                dmamux: None,
                dma: None,
                request: None,
            },
        ],
        interrupts: &[
            PeripheralInterrupt {
                signal: "BRK",
                interrupt: "TIM1_TRG_COM_TIM17",
            },
            PeripheralInterrupt {
                signal: "CC",
                interrupt: "TIM1_TRG_COM_TIM17",
            },
            PeripheralInterrupt {
                signal: "COM",
                interrupt: "TIM1_TRG_COM_TIM17",
            },
            PeripheralInterrupt {
                signal: "TRG",
                interrupt: "TIM1_TRG_COM_TIM17",
            },
            PeripheralInterrupt {
                signal: "UP",
                interrupt: "TIM1_TRG_COM_TIM17",
            },
        ],
    },
    Peripheral {
        name: "TIM2",
        address: 1073741824,
        registers: Some(
            PeripheralRegisters {
                kind: "timer",
                version: "v1",
                block: "TIM_GP32",
                ir: &timer::REGISTERS,
            },
        ),
        rcc: Some(
            PeripheralRcc {
                clock: "pclk1_tim",
                enable: Some(
                    PeripheralRccRegister {
                        register: "apb1enr",
                        field: "tim2en",
                    },
                ),
                reset: Some(
                    PeripheralRccRegister {
                        register: "apb1rstr",
                        field: "tim2rst",
                    },
                ),
                mux: Some(
                    PeripheralRccRegister {
                        register: "cfgr3",
                        field: "tim2sw",
                    },
                ),
                stop_mode: StopMode::Stop1,
            },
        ),
        pins: &[
            PeripheralPin {
                pin: "PA0",
                signal: "CH1",
                af: Some(
                    1,
                ),
            },
            PeripheralPin {
                pin: "PA0",
                signal: "ETR",
                af: Some(
                    1,
                ),
            },
            PeripheralPin {
                pin: "PA1",
                signal: "CH2",
                af: Some(
                    1,
                ),
            },
            PeripheralPin {
                pin: "PA10",
                signal: "CH4",
                af: Some(
                    10,
                ),
            },
            PeripheralPin {
                pin: "PA15",
                signal: "CH1",
                af: Some(
                    1,
                ),
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
                af: Some(
                    2,
                ),
            },
            PeripheralPin {
                pin: "PC9",
                signal: "CH4",
                af: Some(
                    2,
                ),
            },
            PeripheralPin {
                pin: "PD2",
                signal: "ETR",
                af: Some(
                    2,
                ),
            },
            PeripheralPin {
                pin: "PE2",
                signal: "CH1",
                af: Some(
                    2,
                ),
            },
            PeripheralPin {
                pin: "PE3",
                signal: "CH2",
                af: Some(
                    2,
                ),
            },
            PeripheralPin {
                pin: "PE4",
                signal: "CH3",
                af: Some(
                    2,
                ),
            },
            PeripheralPin {
                pin: "PE5",
                signal: "CH4",
                af: Some(
                    2,
                ),
            },
        ],
        dma_channels: &[
            PeripheralDmaChannel {
                signal: "CH3",
                channel: Some(
                    "DMA1_CH2",
                ),
                dmamux: None,
                dma: None,
                request: None,
            },
            PeripheralDmaChannel {
                signal: "CH4",
                channel: Some(
                    "DMA1_CH3",
                ),
                dmamux: None,
                dma: None,
                request: None,
            },
            PeripheralDmaChannel {
                signal: "UP",
                channel: Some(
                    "DMA1_CH3",
                ),
                dmamux: None,
                dma: None,
                request: None,
            },
            PeripheralDmaChannel {
                signal: "CH1",
                channel: Some(
                    "DMA1_CH6",
                ),
                dmamux: None,
                dma: None,
                request: None,
            },
            PeripheralDmaChannel {
                signal: "TRIG",
                channel: Some(
                    "DMA1_CH6",
                ),
                dmamux: None,
                dma: None,
                request: None,
            },
        ],
        interrupts: &[
            PeripheralInterrupt {
                signal: "BRK",
                interrupt: "TIM3",
            },
            PeripheralInterrupt {
                signal: "CC",
                interrupt: "TIM3",
            },
            PeripheralInterrupt {
                signal: "COM",
                interrupt: "TIM3",
            },
            PeripheralInterrupt {
                signal: "TRG",
                interrupt: "TIM3",
            },
            PeripheralInterrupt {
                signal: "UP",
                interrupt: "TIM3",
            },
        ],
    },
    Peripheral {
        name: "TIM4",
        address: 1073743872,
        registers: Some(
            PeripheralRegisters {
                kind: "timer",
                version: "v1",
                block: "TIM_GP16",
                ir: &timer::REGISTERS,
            },
        ),
        rcc: Some(
            PeripheralRcc {
                clock: "pclk1_tim",
                enable: Some(
                    PeripheralRccRegister {
                        register: "apb1enr",
                        field: "tim4en",
                    },
                ),
                reset: Some(
                    PeripheralRccRegister {
                        register: "apb1rstr",
                        field: "tim4rst",
                    },
                ),
                mux: None,
                stop_mode: StopMode::Stop1,
            },
        ),
        pins: &[
            PeripheralPin {
                pin: "PA11",
                signal: "CH1",
                af: Some(
                    10,
                ),
            },
            PeripheralPin {
                pin: "PA12",
                signal: "CH2",
                af: Some(
                    10,
                ),
            },
            PeripheralPin {
                pin: "PA13",
                signal: "CH3",
                af: Some(
                    10,
                ),
            },
            PeripheralPin {
                pin: "PA8",
                signal: "ETR",
                af: Some(
                    10,
                ),
            },
            PeripheralPin {
                pin: "PB3",
                signal: "ETR",
                af: Some(
                    2,
                ),
            },
            PeripheralPin {
                pin: "PB6",
                signal: "CH1",
                af: Some(
                    2,
                ),
            },
            PeripheralPin {
                pin: "PB7",
                signal: "CH2",
                af: Some(
                    2,
                ),
            },
            PeripheralPin {
                pin: "PB8",
                signal: "CH3",
                af: Some(
                    2,
                ),
            },
            PeripheralPin {
                pin: "PB9",
                signal: "CH4",
                af: Some(
                    2,
                ),
            },
            PeripheralPin {
                pin: "PD12",
                signal: "CH1",
                af: Some(
                    2,
                ),
            },
            PeripheralPin {
                pin: "PD13",
                signal: "CH2",
                af: Some(
                    2,
                ),
            },
            PeripheralPin {
                pin: "PD14",
                signal: "CH3",
                af: Some(
                    2,
                ),
            },
            PeripheralPin {
                pin: "PD15",
                signal: "CH4",
                af: Some(
                    2,
                ),
            },
            PeripheralPin {
                pin: "PE0",
                signal: "ETR",
                af: Some(
                    2,
                ),
            },
            PeripheralPin {
                pin: "PF6",
                signal: "CH4",
                af: Some(
                    2,
                ),
            },
        ],
        dma_channels: &[
            PeripheralDmaChannel {
                signal: "CH1",
                channel: Some(
                    "DMA1_CH1",
                ),
                dmamux: None,
                dma: None,
                request: None,
            },
            PeripheralDmaChannel {
                signal: "CH2",
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
